MunyratanakBrorn/Smart-Electrical-Energy-Management-System/Hardware/SmartEnergyMag_System PCB deisgn/12.png

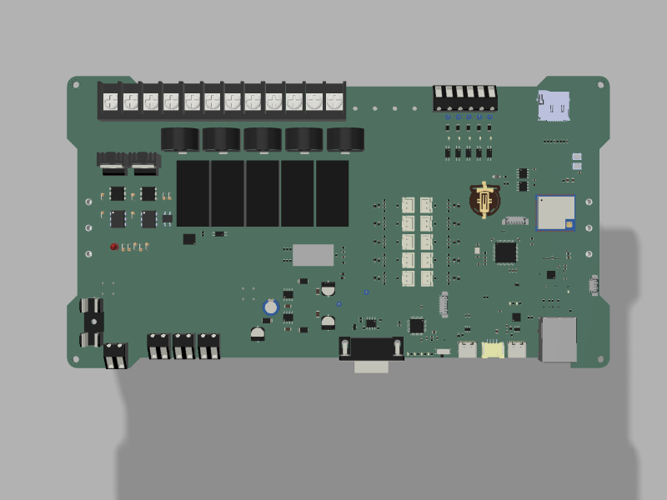
Hardware/SmartEnergyMag_System PCB deisgn/12.png
