MunyratanakBrorn/Smart-Electrical-Energy-Management-System/Hardware/SmartEnergyMag_System PCB deisgn/23.png

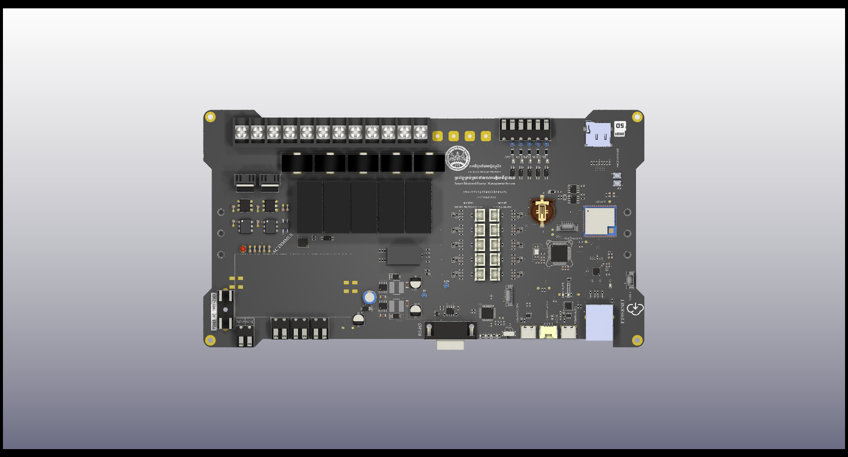
Hardware/SmartEnergyMag_System PCB deisgn/23.png
