MunyratanakBrorn/Smart-Electrical-Energy-Management-System/Hardware/SmartEnergyMag_System PCB deisgn/33.png

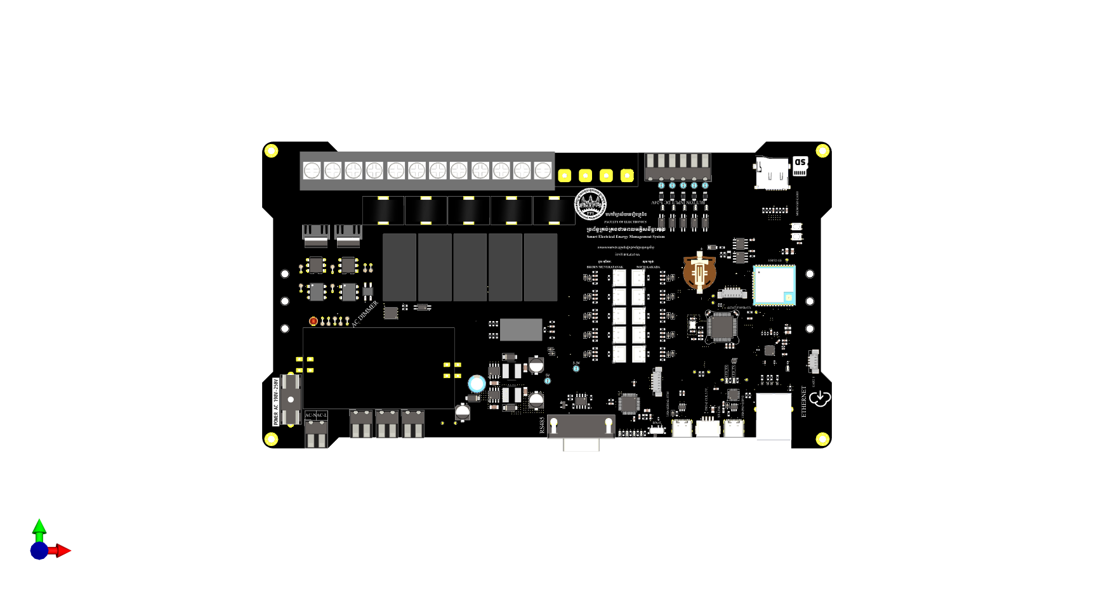
Hardware/SmartEnergyMag_System PCB deisgn/33.png
