MunyratanakBrorn/Smart-Electrical-Energy-Management-System/Hardware/SmartEnergyMag_System PCB deisgn/66.png

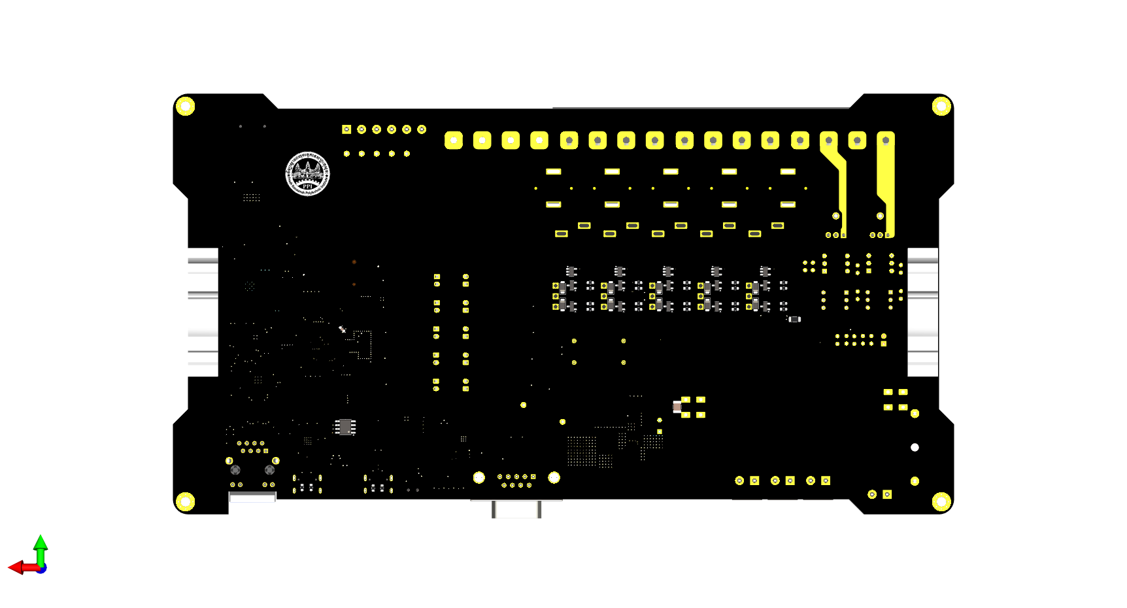
Hardware/SmartEnergyMag_System PCB deisgn/66.png
