MunyratanakBrorn/Smart-Electrical-Energy-Management-System/Hardware/SmartEnergyMag_System PCB deisgn/77.png

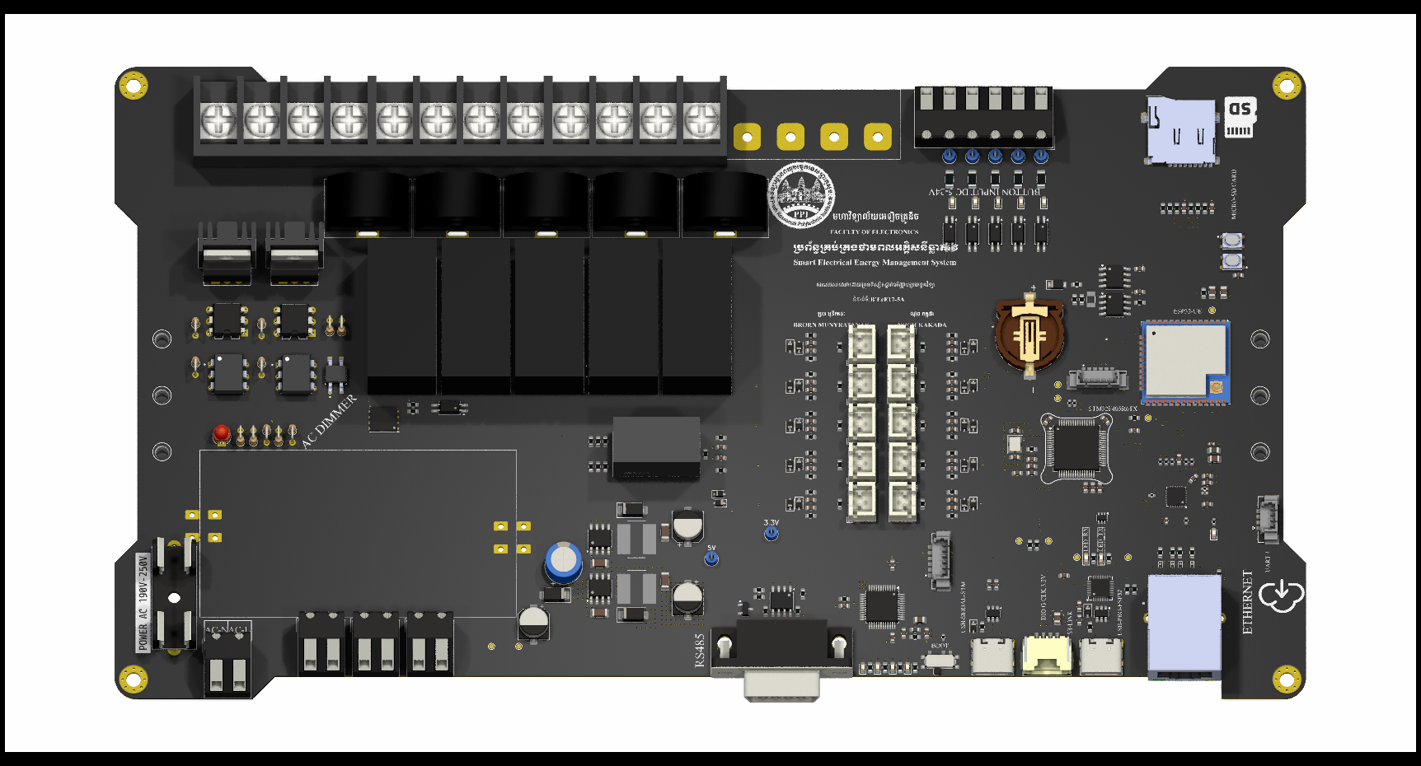
Hardware/SmartEnergyMag_System PCB deisgn/77.png
