MunyratanakBrorn/Smart-Electrical-Energy-Management-System/Hardware/SmartEnergyMag_System PCB deisgn/SmartEnergyMag_System4.png

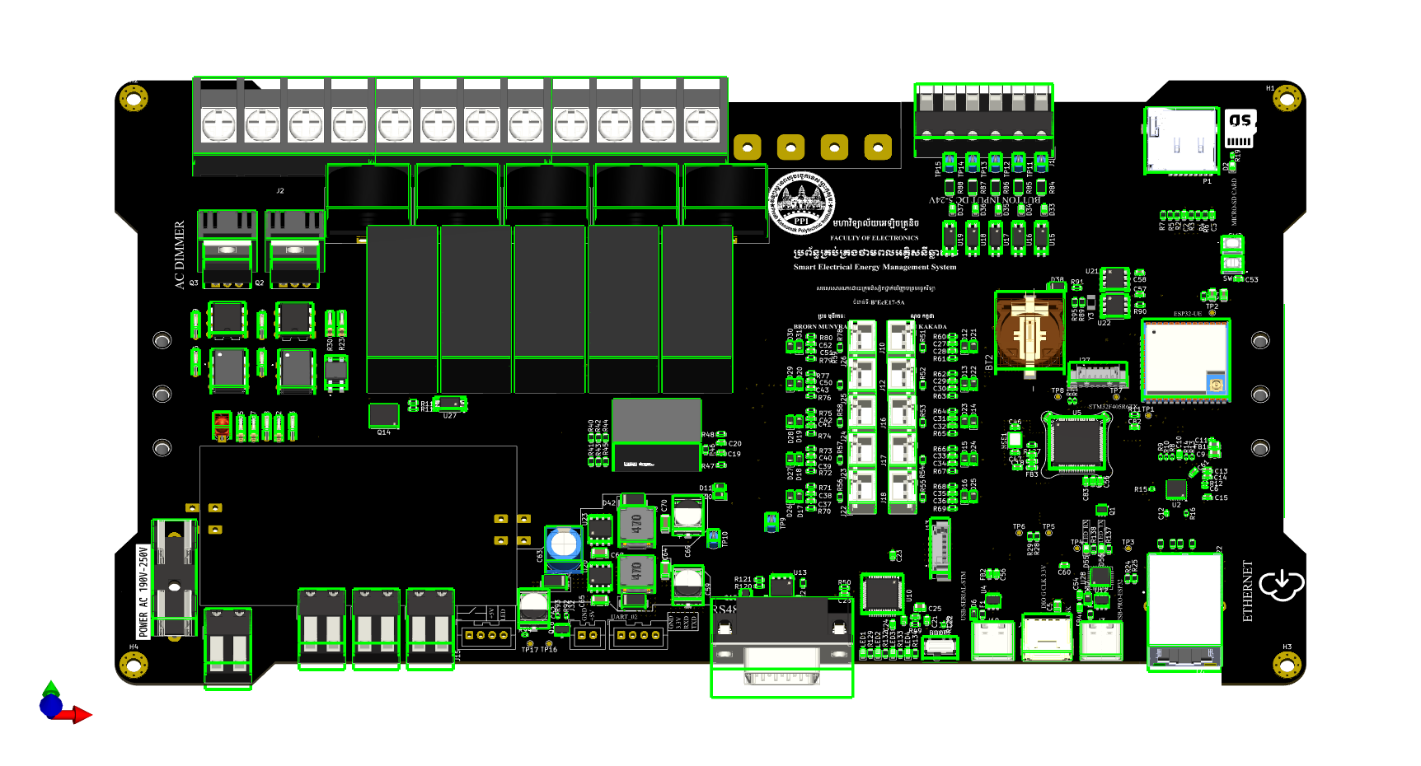
Hardware/SmartEnergyMag_System PCB deisgn/SmartEnergyMag_System4.png
