MunyratanakBrorn/Smart-Electrical-Energy-Management-System/System Overview/Hardware specification.png

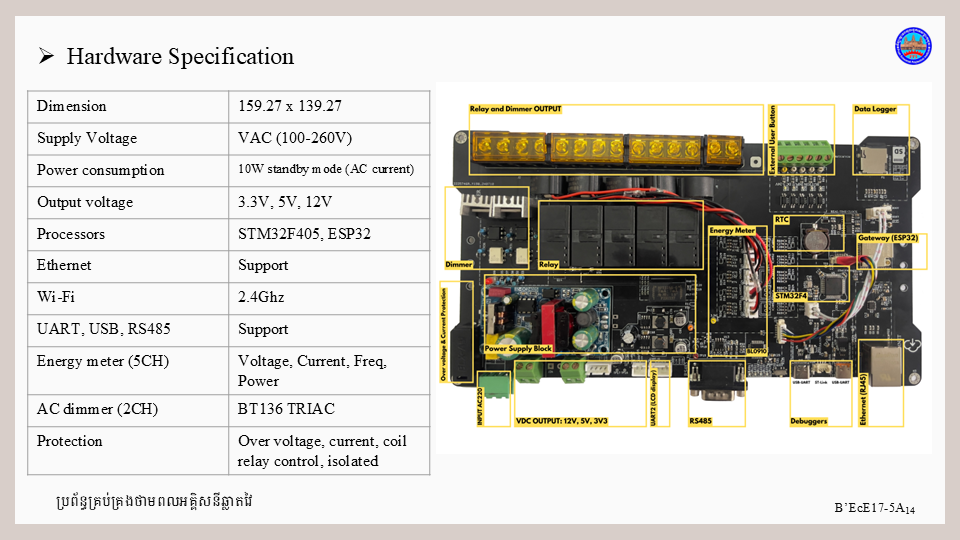
System Overview/Hardware specification.png
