MunyratanakBrorn/Smart-Electrical-Energy-Management-System/Hardware/SmartEnergyMag_System PCB deisgn/BL0940.kicad_sch

## KiCad design Hardware/SmartEnergyMag_System PCB deisgn/BL0940.kicad_sch (2024-08-28)

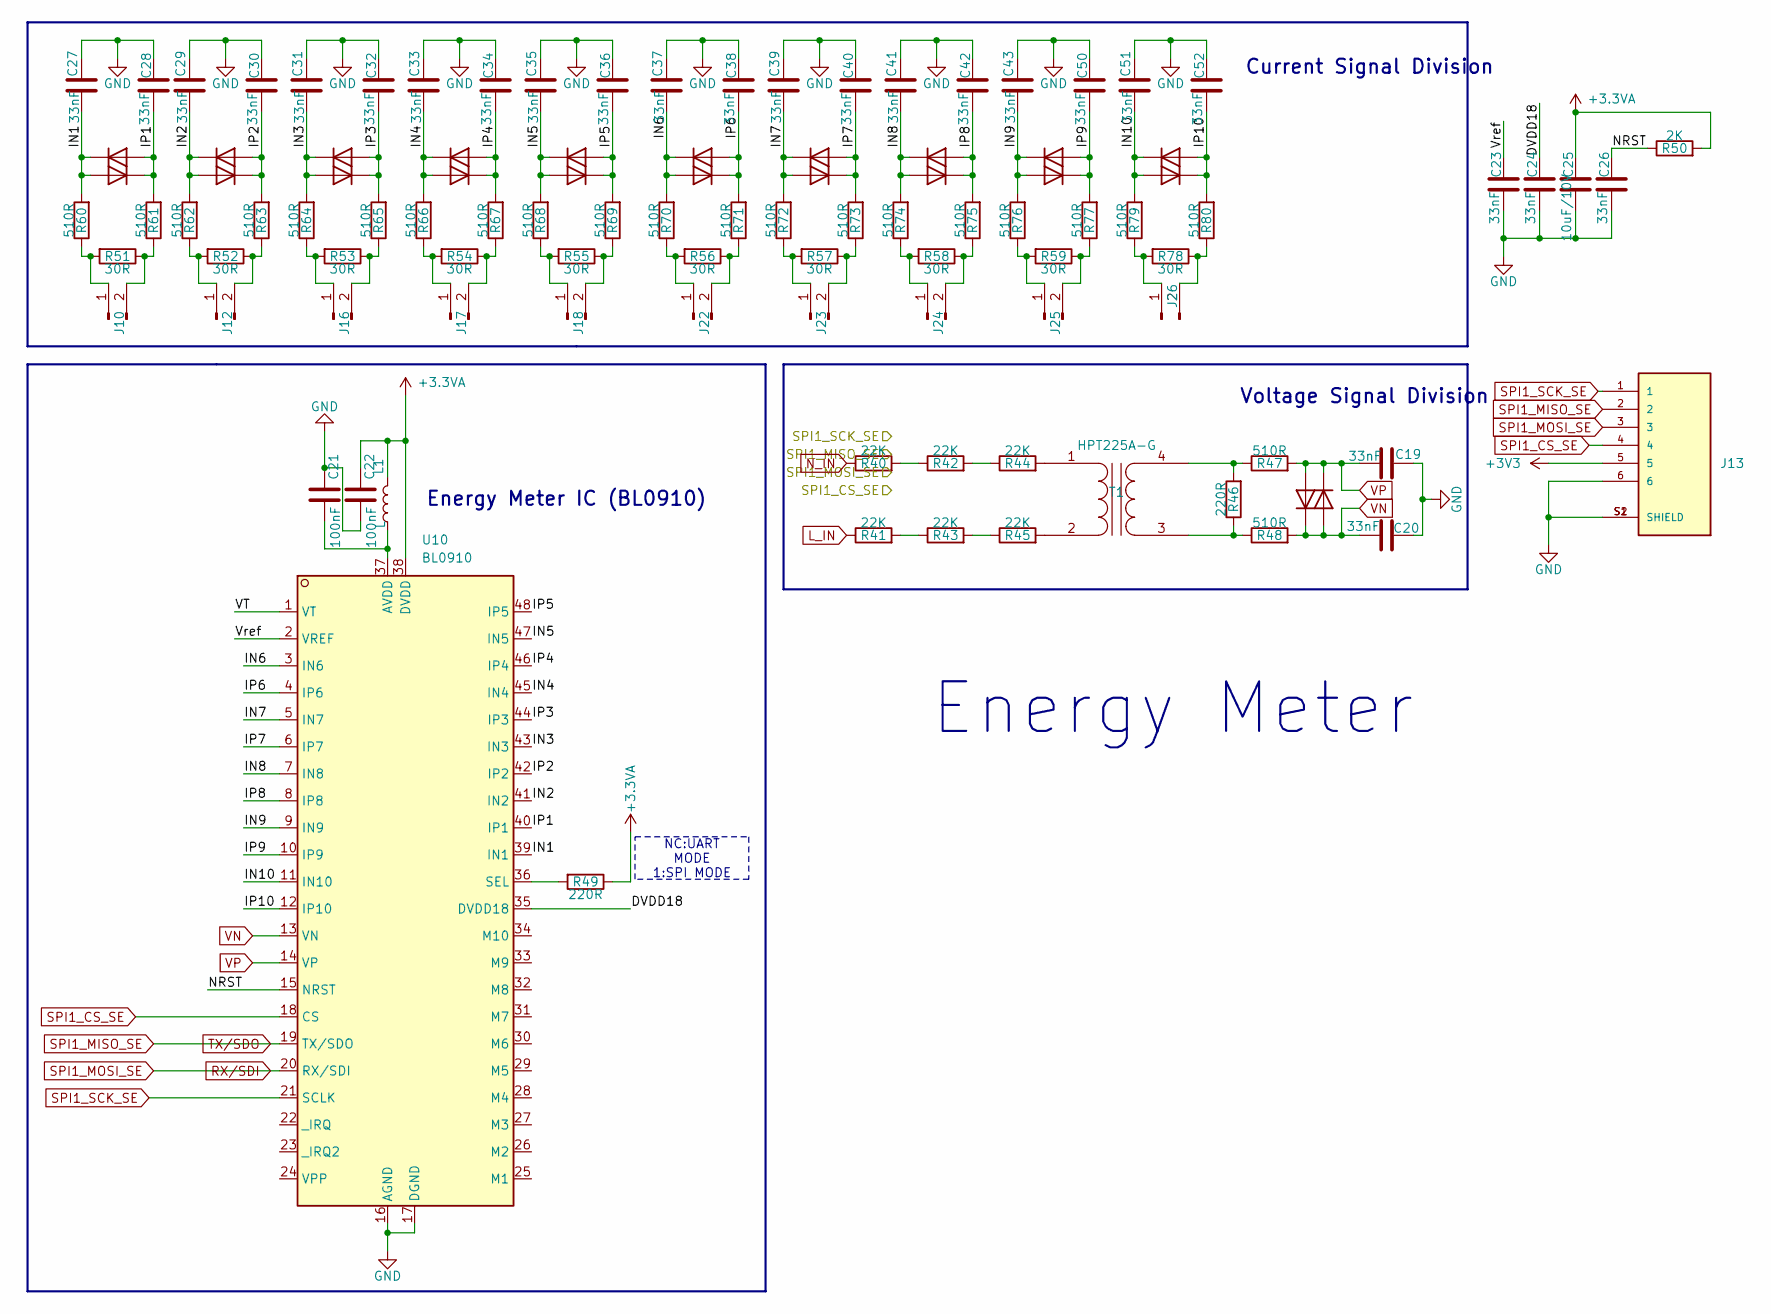
[picture p52: schematic BL0940.kicad_sch]

Parts:
C19, C20, C23, C24, C26, C27, C28, C29, C30, C31, C32, C33, C34, C35, C36, C37, C38, C39, C40, C41, C42, C43, C50, C51, C52: 33nF; C_0603_1608Metric
C21, C22: 100nF; C_0603_1608Metric
C25: 10uF/10V; C_0805_2012Metric
D10, D11, D12, D13, D14, D15, D16, D17, D18, D19, D20, D21, D22, D23, D24, D25, D26, D27, D28, D29, D30, D31: 1N4148WS; D_SOD-323
J10, J12, J16, J17, J18, J22, J23, J24, J25, J26: Conn_01x02_Pin; JST_XH_B2B-XH-A_1x02_P2.50mm_Vertical
J13: 0533980671; MOLEX_0533980671; PARTREV A
L1: L; L_0603_1608Metric
R40, R41, R42, R43, R44, R45: 22K; R_0603_1608Metric
R46, R49: 220R; R_0603_1608Metric
R47, R48, R60, R61, R62, R63, R64, R65, R66, R67, R68, R69, R70, R71, R72, R73, R74, R75, R76, R77, R79, R80: 510R; R_0603_1608Metric
R50: 2K; R_0603_1608Metric
R51, R52, R53, R54, R55, R56, R57, R58, R59, R78: 30R; R_0603_1608Metric
T1: HPT225A-G
U10: BL0910; LQFP-48_7x7mm_P0.5mm

Connections:
+3.3VA: C22.1, C25.2, L1.2, R49.1, R50.2, U10.38 (DVDD)
+3V3: J13.5
DVDD18: C24.2, U10.35 (DVDD18)
GND: C19.2, C20.2, C21.1, C22.2, C23.1, C24.1, C25.1, C26.1, C27.2, C28.2, C29.2, C30.2, C31.2, C32.2, C33.2, C34.2, C35.2, C36.2, C37.2, C38.2, C39.2, C40.2, C41.2, C42.2, C43.2, C50.2, C51.2, C52.2, J13.6, J13.S1 (SHIELD), J13.S2 (SHIELD), U10.16 (AGND), U10.17 (DGND)
IN1: C27.1, D12.2 (A), D21.1 (K), R60.2, U10.39 (IN1)
IN2: C29.1, D13.2 (A), D22.1 (K), R62.2, U10.41 (IN2)
IN3: C31.1, D14.2 (A), D23.1 (K), R64.2, U10.43 (IN3)
IN4: C33.1, D15.2 (A), D24.1 (K), R66.2, U10.45 (IN4)
IN5: C35.1, D16.2 (A), D25.1 (K), R68.2, U10.47 (IN5)
IN6: C37.1, D17.2 (A), D26.1 (K), R70.2, U10.3 (IN6)
IN7: C39.1, D18.2 (A), D27.1 (K), R72.2, U10.5 (IN7)
IN8: C41.1, D19.2 (A), D28.1 (K), R74.2, U10.7 (IN8)
IN9: C43.1, D20.2 (A), D29.1 (K), R76.2, U10.9 (IN9)
IN10: C51.1, D30.2 (A), D31.1 (K), R79.2, U10.11 (IN10)
IP1: C28.1, D12.1 (K), D21.2 (A), R61.2, U10.40 (IP1)
IP2: C30.1, D13.1 (K), D22.2 (A), R63.2, U10.42 (IP2)
IP3: C32.1, D14.1 (K), D23.2 (A), R65.2, U10.44 (IP3)
IP4: C34.1, D15.1 (K), D24.2 (A), R67.2, U10.46 (IP4)
IP5: C36.1, D16.1 (K), D25.2 (A), R69.2, U10.48 (IP5)
IP6: C38.1, D17.1 (K), D26.2 (A), R71.2, U10.4 (IP6)
IP7: C40.1, D18.1 (K), D27.2 (A), R73.2, U10.6 (IP7)
IP8: C42.1, D19.1 (K), D28.2 (A), R75.2, U10.8 (IP8)
IP9: C50.1, D20.1 (K), D29.2 (A), R77.2, U10.10 (IP9)
IP10: C52.1, D30.1 (K), D31.2 (A), R80.2, U10.12 (IP10)
L_IN: R41.1
NRST: C26.2, R50.1, U10.15 (NRST)
N_IN: R40.1
unnamed: C21.2, L1.1, U10.37 (AVDD)
unnamed: J10.1, R51.2, R60.1
unnamed: J10.2, R51.1, R61.1
unnamed: J12.1, R52.2, R62.1
unnamed: J12.2, R52.1, R63.1
unnamed: J16.1, R53.2, R64.1
unnamed: J16.2, R53.1, R65.1
unnamed: J17.1, R54.2, R66.1
unnamed: J17.2, R54.1, R67.1
unnamed: J18.1, R55.2, R68.1
unnamed: J18.2, R55.1, R69.1
unnamed: J22.1, R56.2, R70.1
unnamed: J22.2, R56.1, R71.1
unnamed: J23.1, R57.2, R72.1
unnamed: J23.2, R57.1, R73.1
unnamed: J24.1, R58.2, R74.1
unnamed: J24.2, R58.1, R75.1
unnamed: J25.1, R59.2, R76.1
unnamed: J25.2, R59.1, R77.1
unnamed: J26.1, R78.2, R79.1
unnamed: J26.2, R78.1, R80.1
unnamed: R40.2, R42.1
unnamed: R41.2, R43.1
unnamed: R42.2, R44.1
unnamed: R43.2, R45.1
unnamed: R44.2, T1.1 (AA)
unnamed: R45.2, T1.2 (AB)
unnamed: R46.1, R48.1, T1.3 (SA)
unnamed: R46.2, R47.1, T1.4 (SB)
unnamed: R49.2, U10.36 (SEL)
RX/SDI: J13.3, U10.20 (RX/SDI)
SPI1_CS_SE: J13.4, U10.18 (CS)
SPI1_MISO_SE: J13.2, U10.19 (TX/SDO)
SPI1_SCK_SE: J13.1, U10.21 (SCLK)
VN: C20.1, D10.1 (K), D11.2 (A), R48.2, U10.13 (VN)
VP: C19.1, D10.2 (A), D11.1 (K), R47.2, U10.14 (VP)
VT: U10.1 (VT)
Vref: C23.2, U10.2 (VREF)

Notes on the sheet:
NC:UART MODE 1:SPI MODE
Energy Meter
Voltage Signal Division
Current Signal Division
Energy Meter IC (BL0910)
