MunyratanakBrorn/Smart-Electrical-Energy-Management-System/Hardware/SmartEnergyMag_System PCB deisgn/BL0940_4,5.kicad_sch

## KiCad design Hardware/SmartEnergyMag_System PCB deisgn/BL0940_4,5.kicad_sch (2024-08-28)

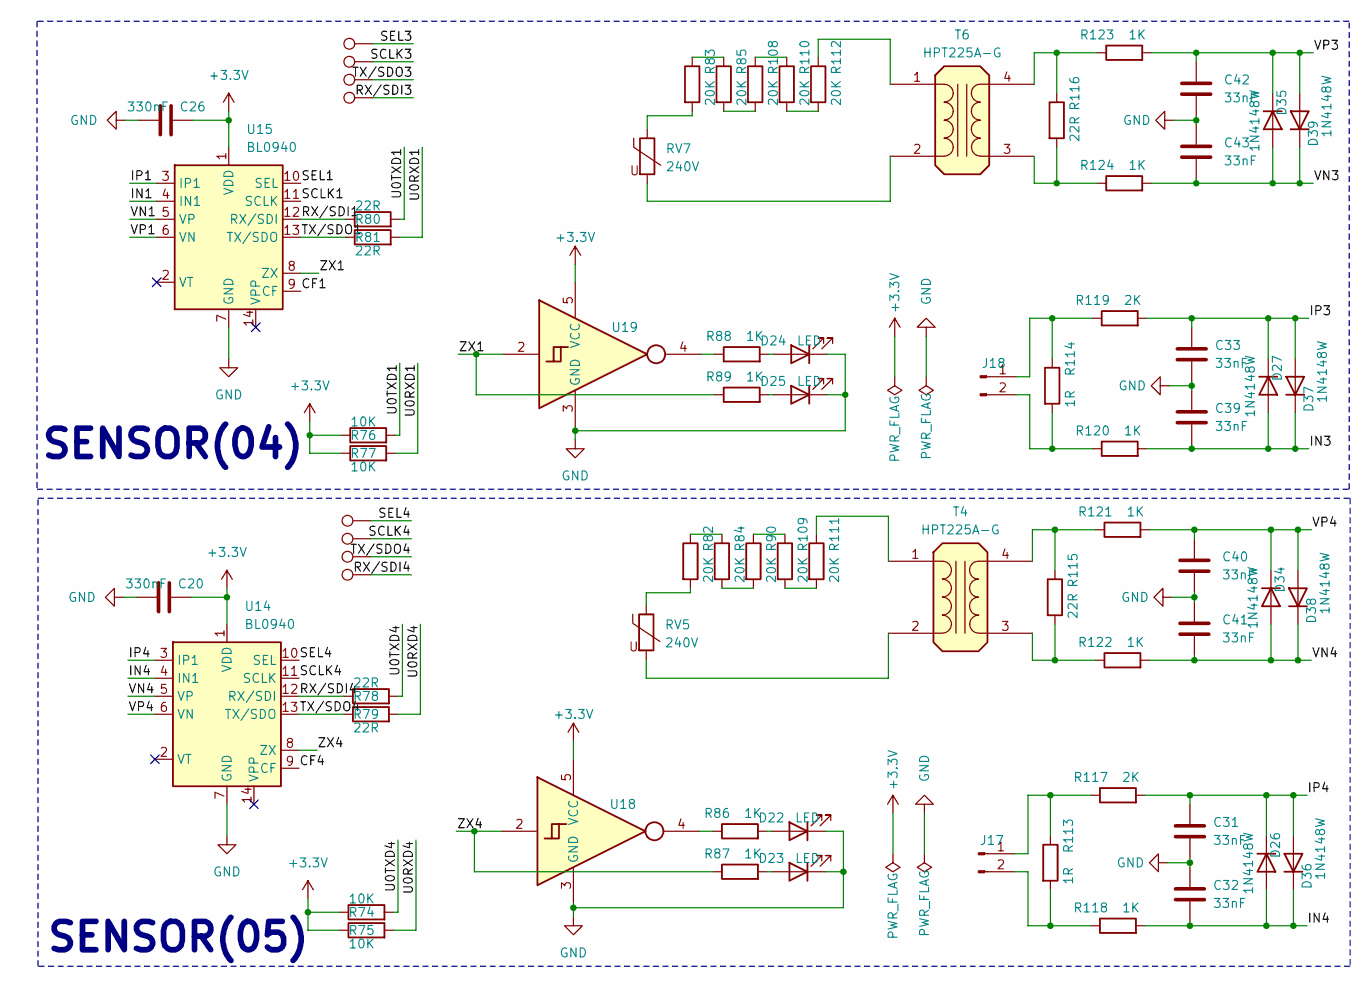
[picture p53: schematic BL0940_4,5.kicad_sch]

Parts:
C20, C26: 330nF; C_0805_2012Metric
C31, C32, C33, C39, C40, C41, C42, C43: 33nF; C_0603_1608Metric
D22, D23, D24, D25: LED; LED_0603_1608Metric
D26, D27, D34, D35, D36, D37, D38, D39: 1N4148W; D_SOD-323
J17, J18: Conn_01x02_Pin; JST_EH_B2B-EH-A_1x02_P2.50mm_Vertical
R74, R75, R76, R77: 10K; R_0603_1608Metric
R78, R79, R80, R81, R115, R116: 22R; R_0603_1608Metric
R82, R83, R84, R85, R90, R108, R109, R110, R111, R112: 20K; R_0603_1608Metric
R86, R87, R88, R89, R118, R120, R121, R122, R123, R124: 1K; R_0603_1608Metric
R113, R114: 1R; R_0603_1608Metric
R117, R119: 2K; R_0603_1608Metric
RV5, RV7: 240V; RV_Disc_D7mm_W3.5mm_P5mm
T4, T6: HPT225A-G
TP13, TP14, TP15, TP16, TP17, TP18, TP25, TP26: TestPoint; TestPoint_Pad_D1.5mm
U14, U15: BL0940; TSSOP-14_4.4x5mm_P0.65mm
U18, U19: SN74LVC1G14DBV; SOT-23-5

Connections:
+3.3V: C20.2, C26.2, R74.1, R75.1, R76.1, R77.1, U14.1 (VDD), U15.1 (VDD), U18.5 (VCC), U19.5 (VCC)
CF1: U15.9 (CF)
CF4: U14.9 (CF)
GND: C20.1, C26.1, C31.2, C32.1, C33.2, C39.1, C40.2, C41.1, C42.2, C43.1, D22.1 (K), D23.1 (K), D24.1 (K), D25.1 (K), U14.7 (GND), U15.7 (GND), U18.3 (GND), U19.3 (GND)
IN1: U15.4 (IN1)
IN3: C39.2, D27.2 (A), D37.1 (K), R120.2
IN4: C32.2, D26.2 (A), D36.1 (K), R118.2, U14.4 (IN1)
IP1: U15.3 (IP1)
IP3: C33.1, D27.1 (K), D37.2 (A), R119.2
IP4: C31.1, D26.1 (K), D36.2 (A), R117.2, U14.3 (IP1)
unnamed: D22.2 (A), R86.2
unnamed: D23.2 (A), R87.2
unnamed: D24.2 (A), R88.2
unnamed: D25.2 (A), R89.2
unnamed: J17.1, R113.1, R117.1
unnamed: J17.2, R113.2, R118.1
unnamed: J18.1, R114.1, R119.1
unnamed: J18.2, R114.2, R120.1
unnamed: R82.1, R84.1
unnamed: R82.2, RV5.1
unnamed: R83.1, R85.1
unnamed: R83.2, RV7.1
unnamed: R84.2, R90.2
unnamed: R86.1, U18.4
unnamed: R88.1, U19.4
unnamed: R108.1, R110.1
unnamed: R85.2, R108.2
unnamed: R90.1, R109.1
unnamed: R109.2, R111.2
unnamed: R110.2, R112.2
unnamed: R111.1, T4.1 (AA)
unnamed: R112.1, T6.1 (AA)
unnamed: R115.1, R121.1, T4.4 (SB)
unnamed: R115.2, R122.1, T4.3 (SA)
unnamed: R116.1, R123.1, T6.4 (SB)
unnamed: R116.2, R124.1, T6.3 (SA)
unnamed: RV5.2, T4.2 (AB)
unnamed: RV7.2, T6.2 (AB)
RX/SDI1: R80.1, U15.12 (RX/SDI)
RX/SDI3: TP26.1
RX/SDI4: R78.1, TP16.1, U14.12 (RX/SDI)
SCLK1: U15.11 (SCLK)
SCLK3: TP18.1
SCLK4: TP14.1, U14.11 (SCLK)
SEL1: U15.10 (SEL)
SEL3: TP17.1
SEL4: TP13.1, U14.10 (SEL)
TX/SDO1: R81.1, U15.13 (TX/SDO)
TX/SDO3: TP25.1
TX/SDO4: R79.1, TP15.1, U14.13 (TX/SDO)
U0RXD1: R77.2, R81.2
U0RXD4: R75.2, R79.2
U0TXD1: R76.2, R80.2
U0TXD4: R74.2, R78.2
VN1: U15.5 (VP)
VN3: C43.2, D35.2 (A), D39.1 (K), R124.2
VN4: C41.2, D34.2 (A), D38.1 (K), R122.2, U14.5 (VP)
VP1: U15.6 (VN)
VP3: C42.1, D35.1 (K), D39.2 (A), R123.2
VP4: C40.1, D34.1 (K), D38.2 (A), R121.2, U14.6 (VN)
ZX1: R89.1, U15.8 (ZX), U19.2
ZX4: R87.1, U14.8 (ZX), U18.2

Notes on the sheet:
SENSOR(05)
SENSOR(04)
