MunyratanakBrorn/Smart-Electrical-Energy-Management-System/Hardware/SmartEnergyMag_System PCB deisgn/BUTTON-INPUT.kicad_sch

## KiCad design Hardware/SmartEnergyMag_System PCB deisgn/BUTTON-INPUT.kicad_sch (2024-08-28)

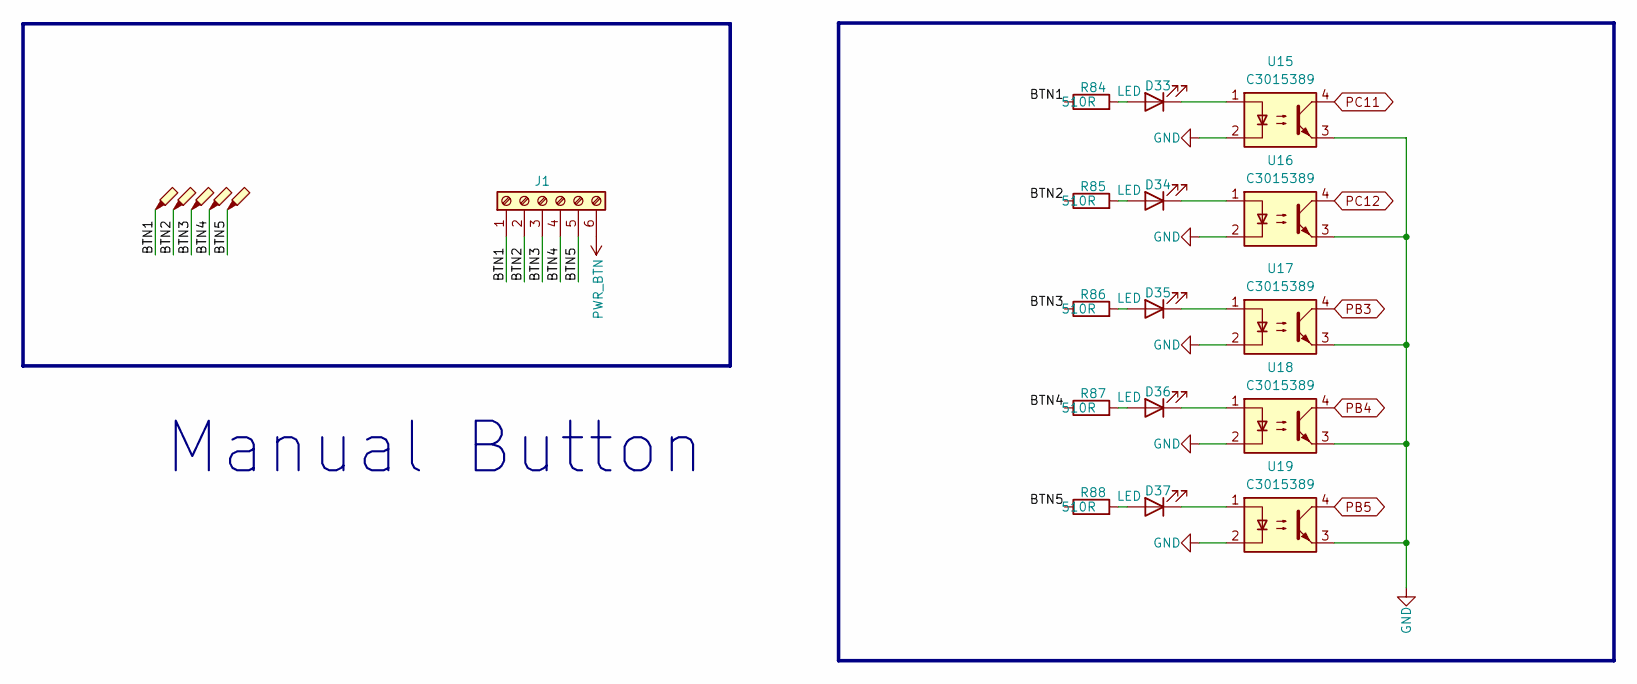
[picture p54: schematic BUTTON-INPUT.kicad_sch]

Parts:
D33, D34, D35, D36, D37: LED; LED_0603_1608Metric
J1: Screw_Terminal_01x06; Altech_AK300_1x06_P5.00mm_45-Degree
R84, R85, R86, R87, R88: 510R; R_1206_3216Metric; JLCPCB Part # C3017298
TP11, TP13, TP14, TP15: C5199900; TestPoint_Loop_D1.80mm_Drill1.0mm_Beaded; JLCPCB Part # C5277087
TP12: C5199900; TestPoint_Loop_D1.80mm_Drill1.0mm_Beaded
U15, U16, U17, U18, U19: C3015389; SOP-4_4.4x2.6mm_P1.27mm

Connections:
BTN1: J1.1, R84.1, TP11.1
BTN2: J1.2, R85.1, TP12.1
BTN3: J1.3, R86.1, TP13.1
BTN4: J1.4, R87.1, TP14.1
BTN5: J1.5, R88.1, TP15.1
GND: U15.2, U15.3, U16.2, U16.3, U17.2, U17.3, U18.2, U18.3, U19.2, U19.3
unnamed: D33.1 (K), U15.1
unnamed: D33.2 (A), R84.2
unnamed: D34.1 (K), U16.1
unnamed: D34.2 (A), R85.2
unnamed: D35.1 (K), U17.1
unnamed: D35.2 (A), R86.2
unnamed: D36.1 (K), U18.1
unnamed: D36.2 (A), R87.2
unnamed: D37.1 (K), U19.1
unnamed: D37.2 (A), R88.2
PB3: U17.4
PB4: U18.4
PB5: U19.4
PC11: U15.4
PC12: U16.4
PWR_BTN: J1.6

Notes on the sheet:
Manual Button
