MunyratanakBrorn/Smart-Electrical-Energy-Management-System/Hardware/SmartEnergyMag_System PCB deisgn/Buck converter.kicad_sch

## KiCad design Hardware/SmartEnergyMag_System PCB deisgn/Buck converter.kicad_sch (2024-08-28)

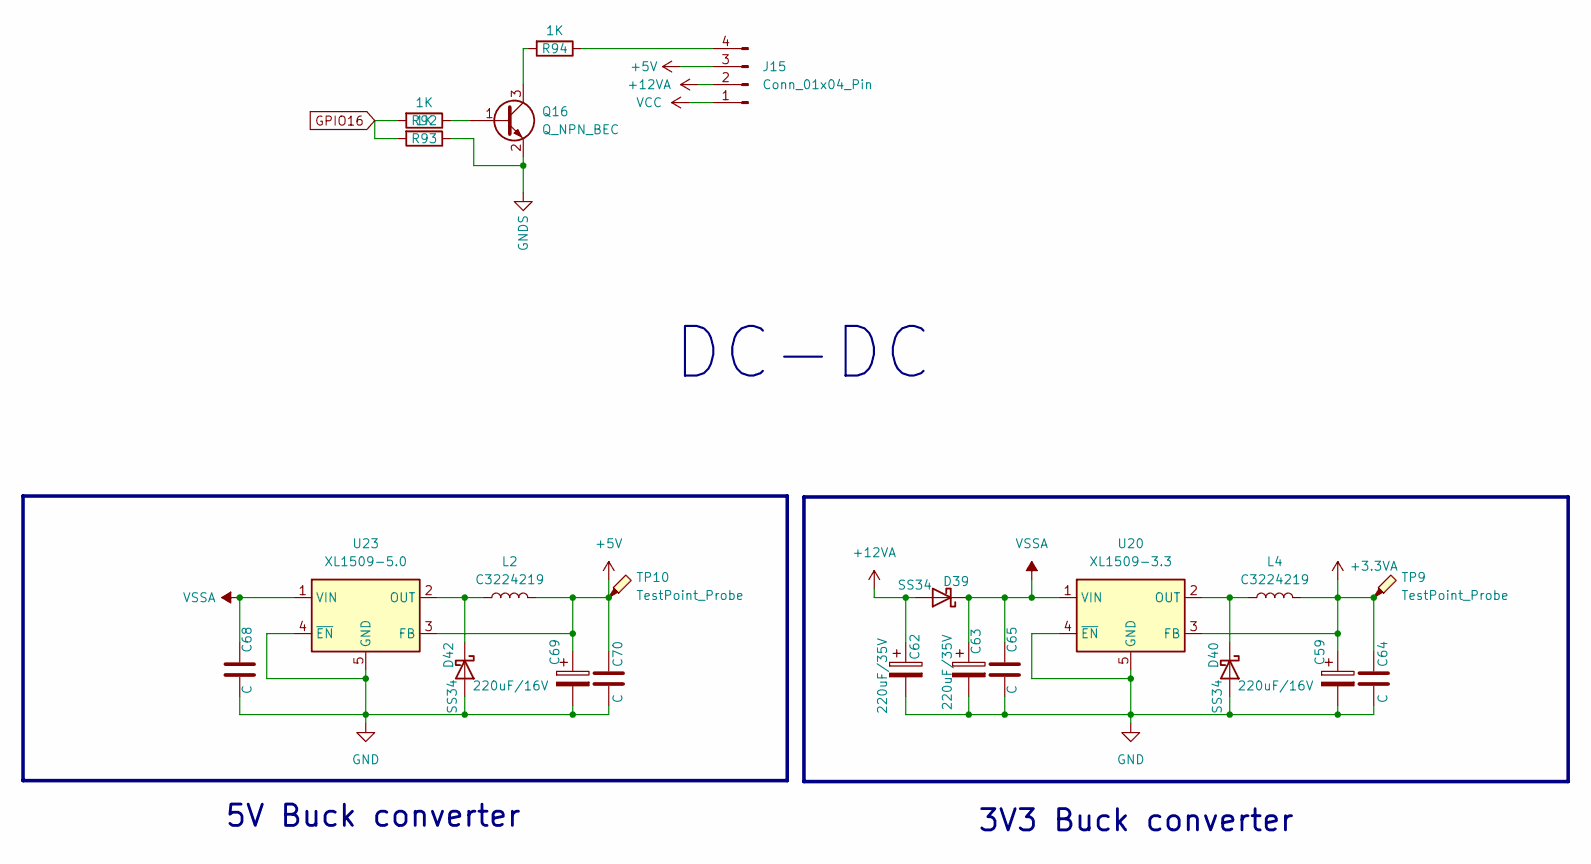
[picture p55: schematic Buck converter.kicad_sch]

Parts:
C59, C69: 220uF/16V; CP_Elec_6.3x4.5; JLCPCB Part # C59918
C62: 220uF/35V; CP_Elec_6.3x4.5; JLCPCB Part # C59918
C63: 220uF/35V; CP_Radial_D8.0mm_P3.80mm; JLCPCB Part # C59918
C64, C65, C68, C70: C; C_1206_3216Metric
D39, D40, D42: SS34; D_SMA
J15: Conn_01x04_Pin; JST_XA_B04B-XASK-1_1x04_P2.50mm_Vertical
L2, L4: C3224219; L_Bourns_SRN8040TA
Q16: Q_NPN_BEC; SOT-23
R92, R93, R94: 1K; R_0402_1005Metric
TP9, TP10: TestPoint_Probe; TestPoint_Loop_D1.80mm_Drill1.0mm_Beaded
U20: XL1509-3.3; SOIC-8_3.9x4.9mm_P1.27mm; JLCPCB Part # C2681226
U23: XL1509-5.0; SOIC-8_3.9x4.9mm_P1.27mm; JLCPCB Part # C2902368

Connections:
+3.3VA: C59.1, C64.1, L4.2, TP9.1, U20.3 (FB)
+5V: C69.1, C70.1, J15.3, L2.2, TP10.1, U23.3 (FB)
+12VA: C62.1, D39.2 (A), J15.2
GND: C59.2, C62.2, C63.2, C64.2, C65.2, C68.2, C69.2, C70.2, D40.2 (A), D42.2 (A), U20.4 (~EN), U20.5 (GND), U20.6 (GND), U20.7 (GND), U20.8 (GND), U23.4 (~EN), U23.5 (GND), U23.6 (GND), U23.7 (GND), U23.8 (GND)
GNDS: Q16.2 (E), R93.1
GPIO16: R92.2, R93.2
unnamed: D40.1 (K), L4.1, U20.2 (OUT)
unnamed: D42.1 (K), L2.1, U23.2 (OUT)
unnamed: J15.4, R94.1
unnamed: Q16.1 (B), R92.1
unnamed: Q16.3 (C), R94.2
VCC: J15.1
VSSA: C63.1, C65.1, C68.1, D39.1 (K), U20.1 (VIN), U23.1 (VIN)

Notes on the sheet:
3V3 Buck converter
DC-DC
5V Buck converter
