MunyratanakBrorn/Smart-Electrical-Energy-Management-System/Hardware/SmartEnergyMag_System PCB deisgn/Dimmer PCB.kicad_sch

## KiCad design Hardware/SmartEnergyMag_System PCB deisgn/Dimmer PCB.kicad_sch (2024-08-28)

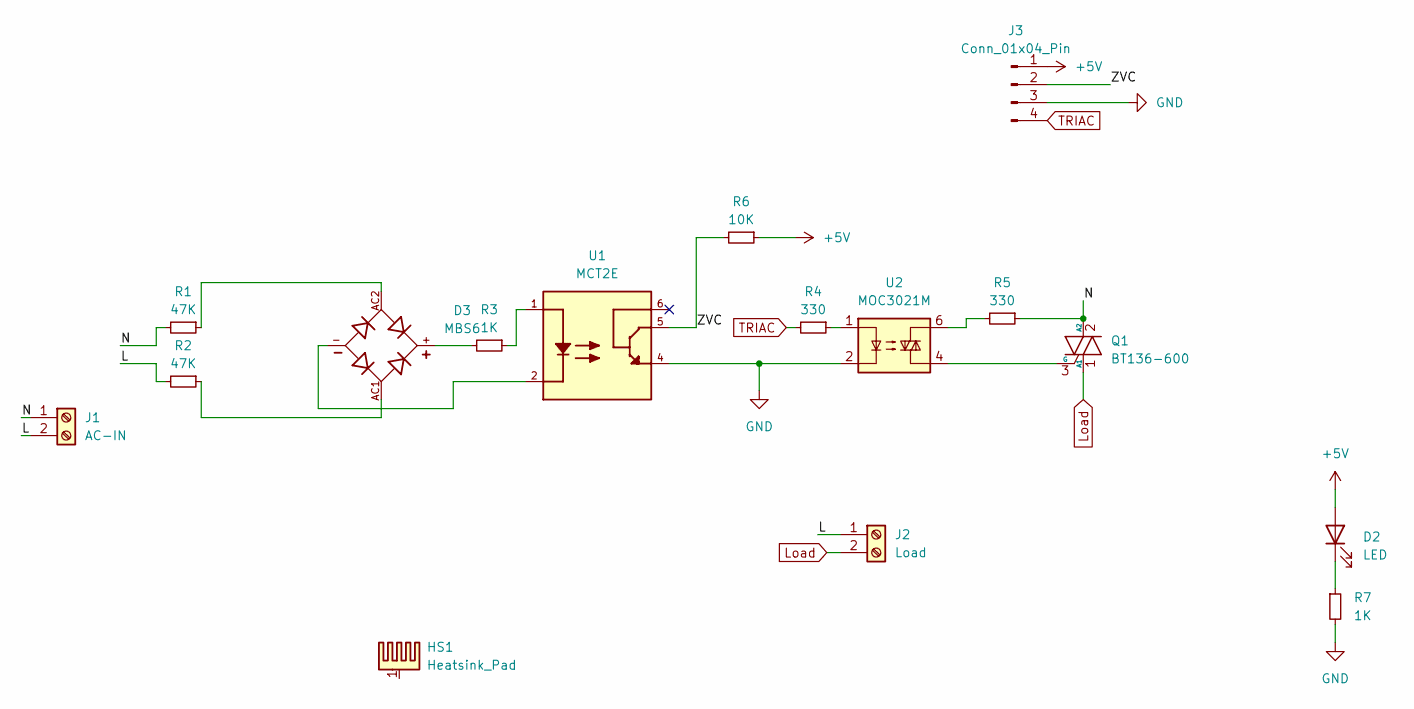
[picture p56: schematic Dimmer PCB.kicad_sch]

Parts:
D2: LED; LED_D3.0mm
D3: MBS6; DIOB_MBS6; PARTREV Q2309
HS1: Heatsink_Pad; HSINK_SK_95_25_STS_TO_220
J1: AC-IN; Altech_AK300_1x02_P5.00mm_45-Degree
J2: Load; Altech_AK300_1x02_P5.00mm_45-Degree
J3: Conn_01x04_Pin; PinHeader_1x04_P2.54mm_Vertical
Q1: BT136-600; TO-220-3_Vertical
R1, R2: 47K; R_Axial_DIN0204_L3.6mm_D1.6mm_P2.54mm_Vertical
R3, R7: 1K; R_Axial_DIN0204_L3.6mm_D1.6mm_P2.54mm_Vertical
R4, R5: 330; R_Axial_DIN0204_L3.6mm_D1.6mm_P2.54mm_Vertical
R6: 10K; R_Axial_DIN0204_L3.6mm_D1.6mm_P2.54mm_Vertical
U1: MCT2E; DIP762W50P254L742H480Q6; PARTREV 7
U2: MOC3021M; DIP-6_W7.62mm

Connections:
+5V: D2.2 (A), J3.1, R6.1
GND: J3.3, R7.2, U1.4, U2.2
L: J1.2, J2.1, R2.2
Load: J2.2, Q1.1 (A1)
N: J1.1, Q1.2 (A2), R1.2, R5.1
unnamed: D2.1 (K), R7.1
unnamed: D3.+, R3.2
unnamed: D3.-, U1.2
unnamed: D3.AC1, R2.1
unnamed: D3.AC2, R1.1
unnamed: Q1.3 (G), U2.4
unnamed: R3.1, U1.1
unnamed: R4.1, U2.1
unnamed: R5.2, U2.6
TRIAC: J3.4, R4.2
ZVC: J3.2, R6.2, U1.5
