MunyratanakBrorn/Smart-Electrical-Energy-Management-System/Hardware/SmartEnergyMag_System PCB deisgn/Dimmer_PCB.kicad_sch

## KiCad design Hardware/SmartEnergyMag_System PCB deisgn/Dimmer_PCB.kicad_sch (2024-08-28)

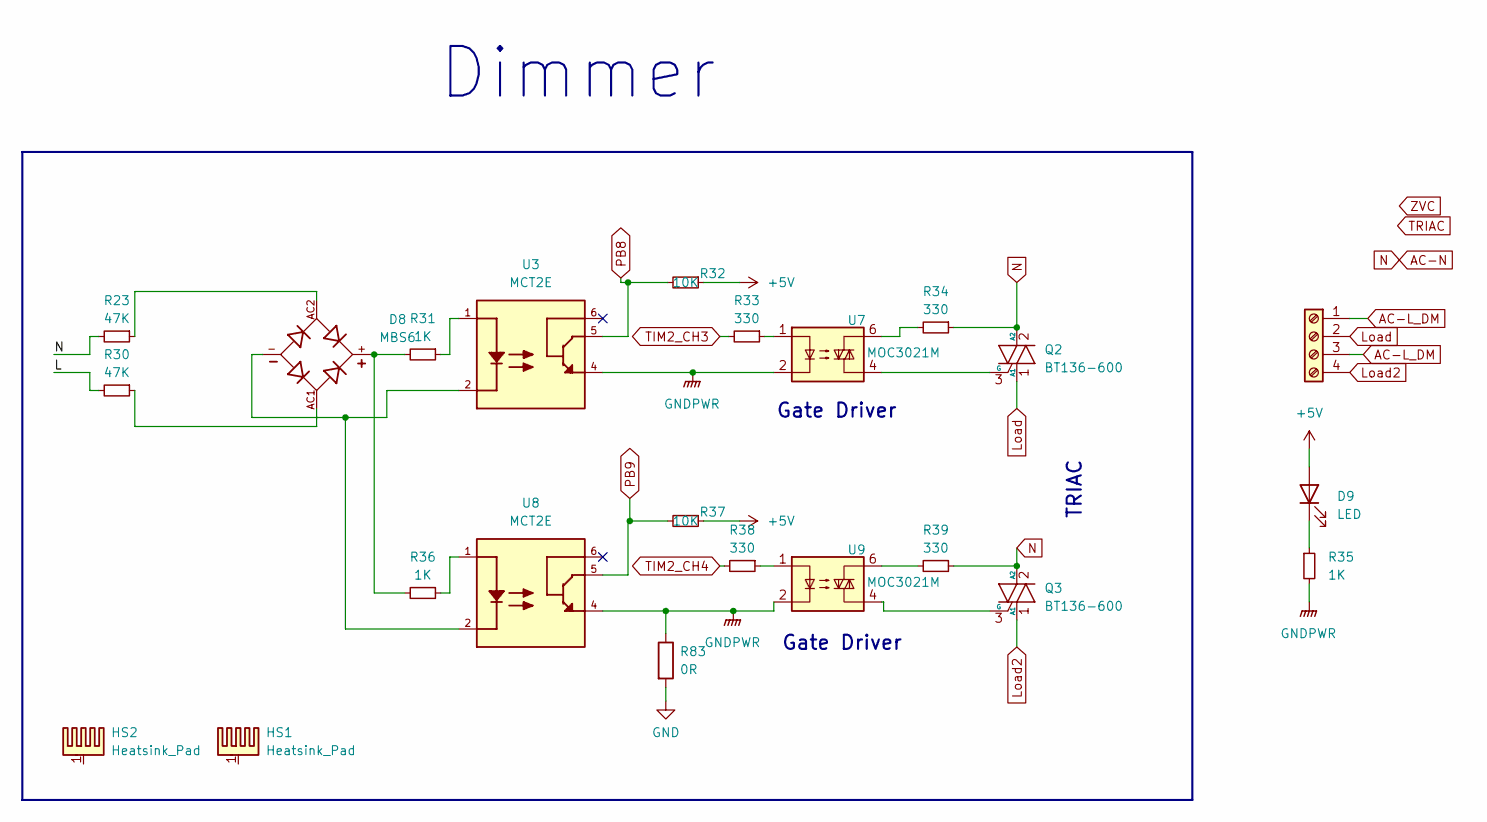
[picture p57: schematic Dimmer_PCB.kicad_sch]

Parts:
D8: MBS6; DIOB_MBS6; PARTREV Q2309
D9: LED; LED_D3.0mm
HS1, HS2: Heatsink_Pad; HSINK_SK_95_25_STS_TO_220
J2: Screw_Terminal_01x04; DBT50G-9.5-4P
Q2, Q3: BT136-600; TO-220-3_Vertical
R23, R30: 47K; R_Axial_DIN0204_L3.6mm_D1.6mm_P2.54mm_Vertical
R31, R35, R36: 1K; R_Axial_DIN0204_L3.6mm_D1.6mm_P2.54mm_Vertical
R32, R37: 10K; R_Axial_DIN0204_L3.6mm_D1.6mm_P2.54mm_Vertical
R33, R34, R38, R39: 330; R_Axial_DIN0204_L3.6mm_D1.6mm_P2.54mm_Vertical
R83: 0R; R_1206_3216Metric
U3, U8: MCT2E; DIP762W50P254L742H480Q6; PARTREV 7
U7, U9: MOC3021M; DIP-6_W7.62mm

Connections:
+5V: D9.2 (A), R32.1, R37.1
AC-L_DM: J2.1, J2.3
AC-N: Q2.2 (A2), Q3.2 (A2), R34.1, R39.1
GND: R83.2
GNDPWR: R35.2, R83.1, U3.4, U7.2, U8.4, U9.2
L: R30.2
Load: J2.2, Q2.1 (A1)
Load2: J2.4, Q3.1 (A1)
N: R23.2
unnamed: D8.+, R31.2, R36.2
unnamed: D8.-, U3.2, U8.2
unnamed: D8.AC1, R30.1
unnamed: D8.AC2, R23.1
unnamed: D9.1 (K), R35.1
unnamed: Q2.3 (G), U7.4
unnamed: Q3.3 (G), U9.4
unnamed: R31.1, U3.1
unnamed: R33.1, U7.1
unnamed: R34.2, U7.6
unnamed: R36.1, U8.1
unnamed: R38.1, U9.1
unnamed: R39.2, U9.6
PB8: R32.2, U3.5
PB9: R37.2, U8.5
TIM2_CH3: R33.2
TIM2_CH4: R38.2

Notes on the sheet:
TRIAC
Gate Driver
Dimmer
