MunyratanakBrorn/Smart-Electrical-Energy-Management-System/Hardware/SmartEnergyMag_System PCB deisgn/Microcontroller.kicad_sch

## KiCad design Hardware/SmartEnergyMag_System PCB deisgn/Microcontroller.kicad_sch (2024-08-28)

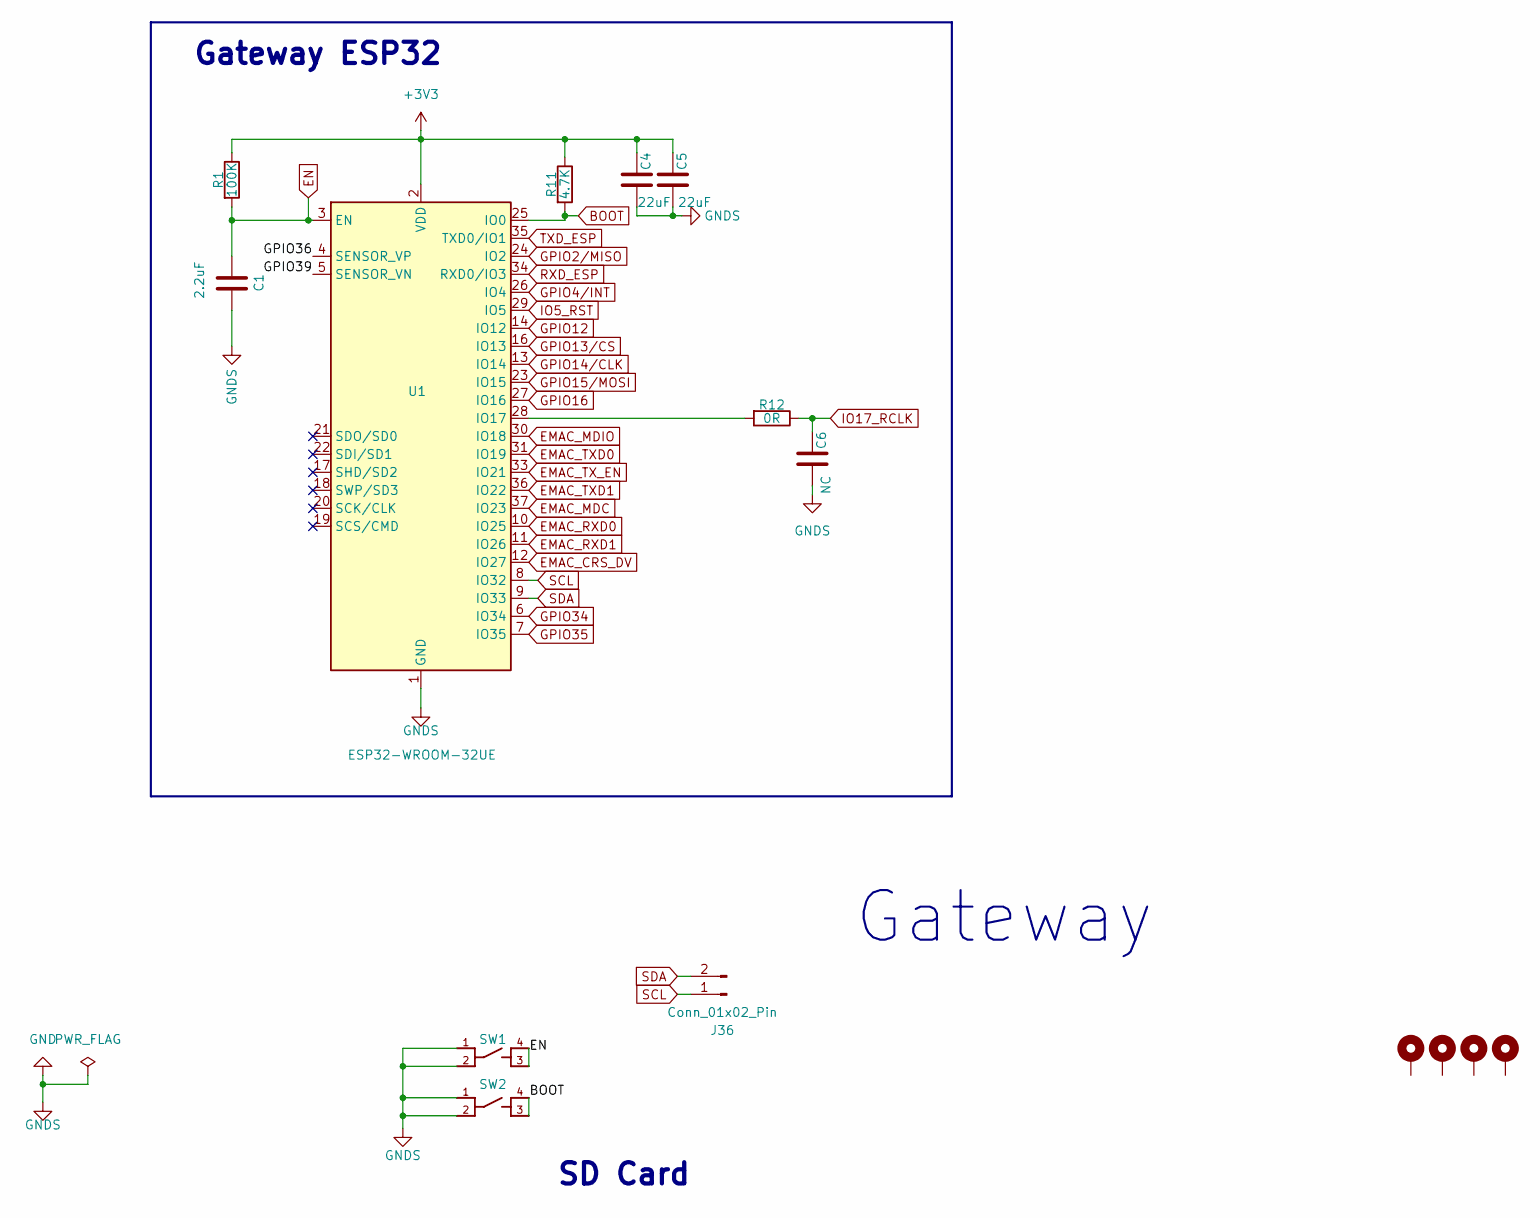
[picture p58: schematic Microcontroller.kicad_sch]

Parts:
C1: 2.2uF; C_0805_2012Metric
C4, C5: 22uF; C_0805_2012Metric
C6: NC; C_0402_1005Metric
H1, H2, H3, H4: MountingHole_Pad; MountingHole_3.2mm_M3_Pad_Via
J36: Conn_01x02_Pin; JST_XA_B02B-XASK-1_1x02_P2.50mm_Vertical
R1: 100K; R_0603_1608Metric
R11: 4.7K; R_0603_1608Metric
R12: 0R; R_0402_1005Metric
SW1, SW2: C221895; SW_PTS810_SJM_250_SMTR_LFS
U1: ESP32-WROOM-32UE; ESP32-WROOM-32U

Connections:
+3V3: C4.1, C5.1, R1.1, R11.1, U1.2 (VDD)
BOOT: R11.2, SW2.3, SW2.4, U1.25 (IO0)
EMAC_CRS_DV: U1.12 (IO27)
EMAC_MDC: U1.37 (IO23)
EMAC_MDIO: U1.30 (IO18)
EMAC_RXD0: U1.10 (IO25)
EMAC_RXD1: U1.11 (IO26)
EMAC_TXD0: U1.31 (IO19)
EMAC_TXD1: U1.36 (IO22)
EMAC_TX_EN: U1.33 (IO21)
EN: C1.1, R1.2, SW1.3, SW1.4, U1.3 (EN)
GND: C1.2, C4.2, C5.2, C6.2, SW1.1, SW1.2, SW2.1, SW2.2, U1.1 (GND), U1.15 (GND), U1.38 (GND), U1.39 (GND)
GPIO2/MISO: U1.24 (IO2)
GPIO4/INT: U1.26 (IO4)
GPIO12: U1.14 (IO12)
GPIO13/CS: U1.16 (IO13)
GPIO14/CLK: U1.13 (IO14)
GPIO15/MOSI: U1.23 (IO15)
GPIO16: U1.27 (IO16)
GPIO34: U1.6 (IO34)
GPIO35: U1.7 (IO35)
GPIO36: U1.4 (SENSOR_VP)
GPIO39: U1.5 (SENSOR_VN)
IO5_RST: U1.29 (IO5)
IO17_RCLK: C6.1, R12.1
unnamed: R12.2, U1.28 (IO17)
RXD_ESP: U1.34 (RXD0/IO3)
SCL: J36.1, U1.8 (IO32)
SDA: J36.2, U1.9 (IO33)
TXD_ESP: U1.35 (TXD0/IO1)

Notes on the sheet:
SD Card
Gateway
Gateway ESP32
