MunyratanakBrorn/Smart-Electrical-Energy-Management-System/Hardware/SmartEnergyMag_System PCB deisgn/Power.kicad_sch

## KiCad design Hardware/SmartEnergyMag_System PCB deisgn/Power.kicad_sch (2024-08-28)

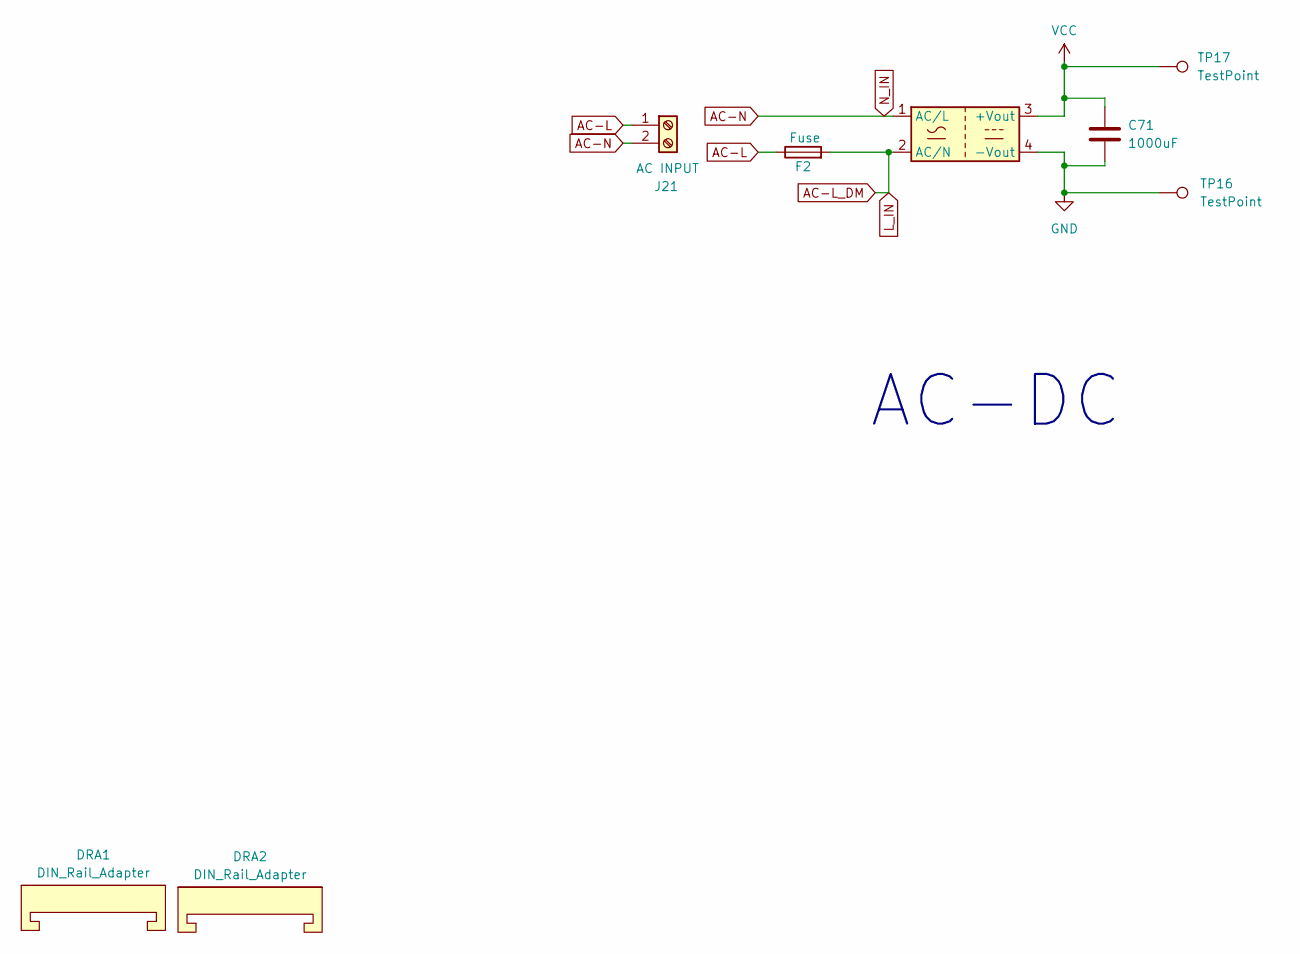
[picture p59: schematic Power.kicad_sch]

Parts:
C71: 1000uF; C_1210_3225Metric
DRA1, DRA2: DIN_Rail_Adapter; DINRailAdapter_3xM3_PhoenixContact_1201578
F2: Fuse; Fuseholder_Cylinder-5x20mm_Schurter_0031_8201_Horizontal_Op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
J21: AC INPUT; Altech_AK300_1x02_P5.00mm_45-Degree
PS1: HLK-12M05A; AC-DC
TP16, TP17: TestPoint; TestPoint_Pad_D1.0mm

Connections:
AC-L: F2.1, J21.1
AC-L_DM: F2.2, PS1.2 (AC/N)
AC-N: J21.2, PS1.1 (AC/L)
GND: C71.1, PS1.4 (-Vout), TP16.1
VCC: C71.2, PS1.3 (+Vout), TP17.1

Notes on the sheet:
AC-DC
