MunyratanakBrorn/Smart-Electrical-Energy-Management-System/Hardware/SmartEnergyMag_System PCB deisgn/RELAY_5CH.kicad_sch

## KiCad design Hardware/SmartEnergyMag_System PCB deisgn/RELAY_5CH.kicad_sch (2024-08-28)

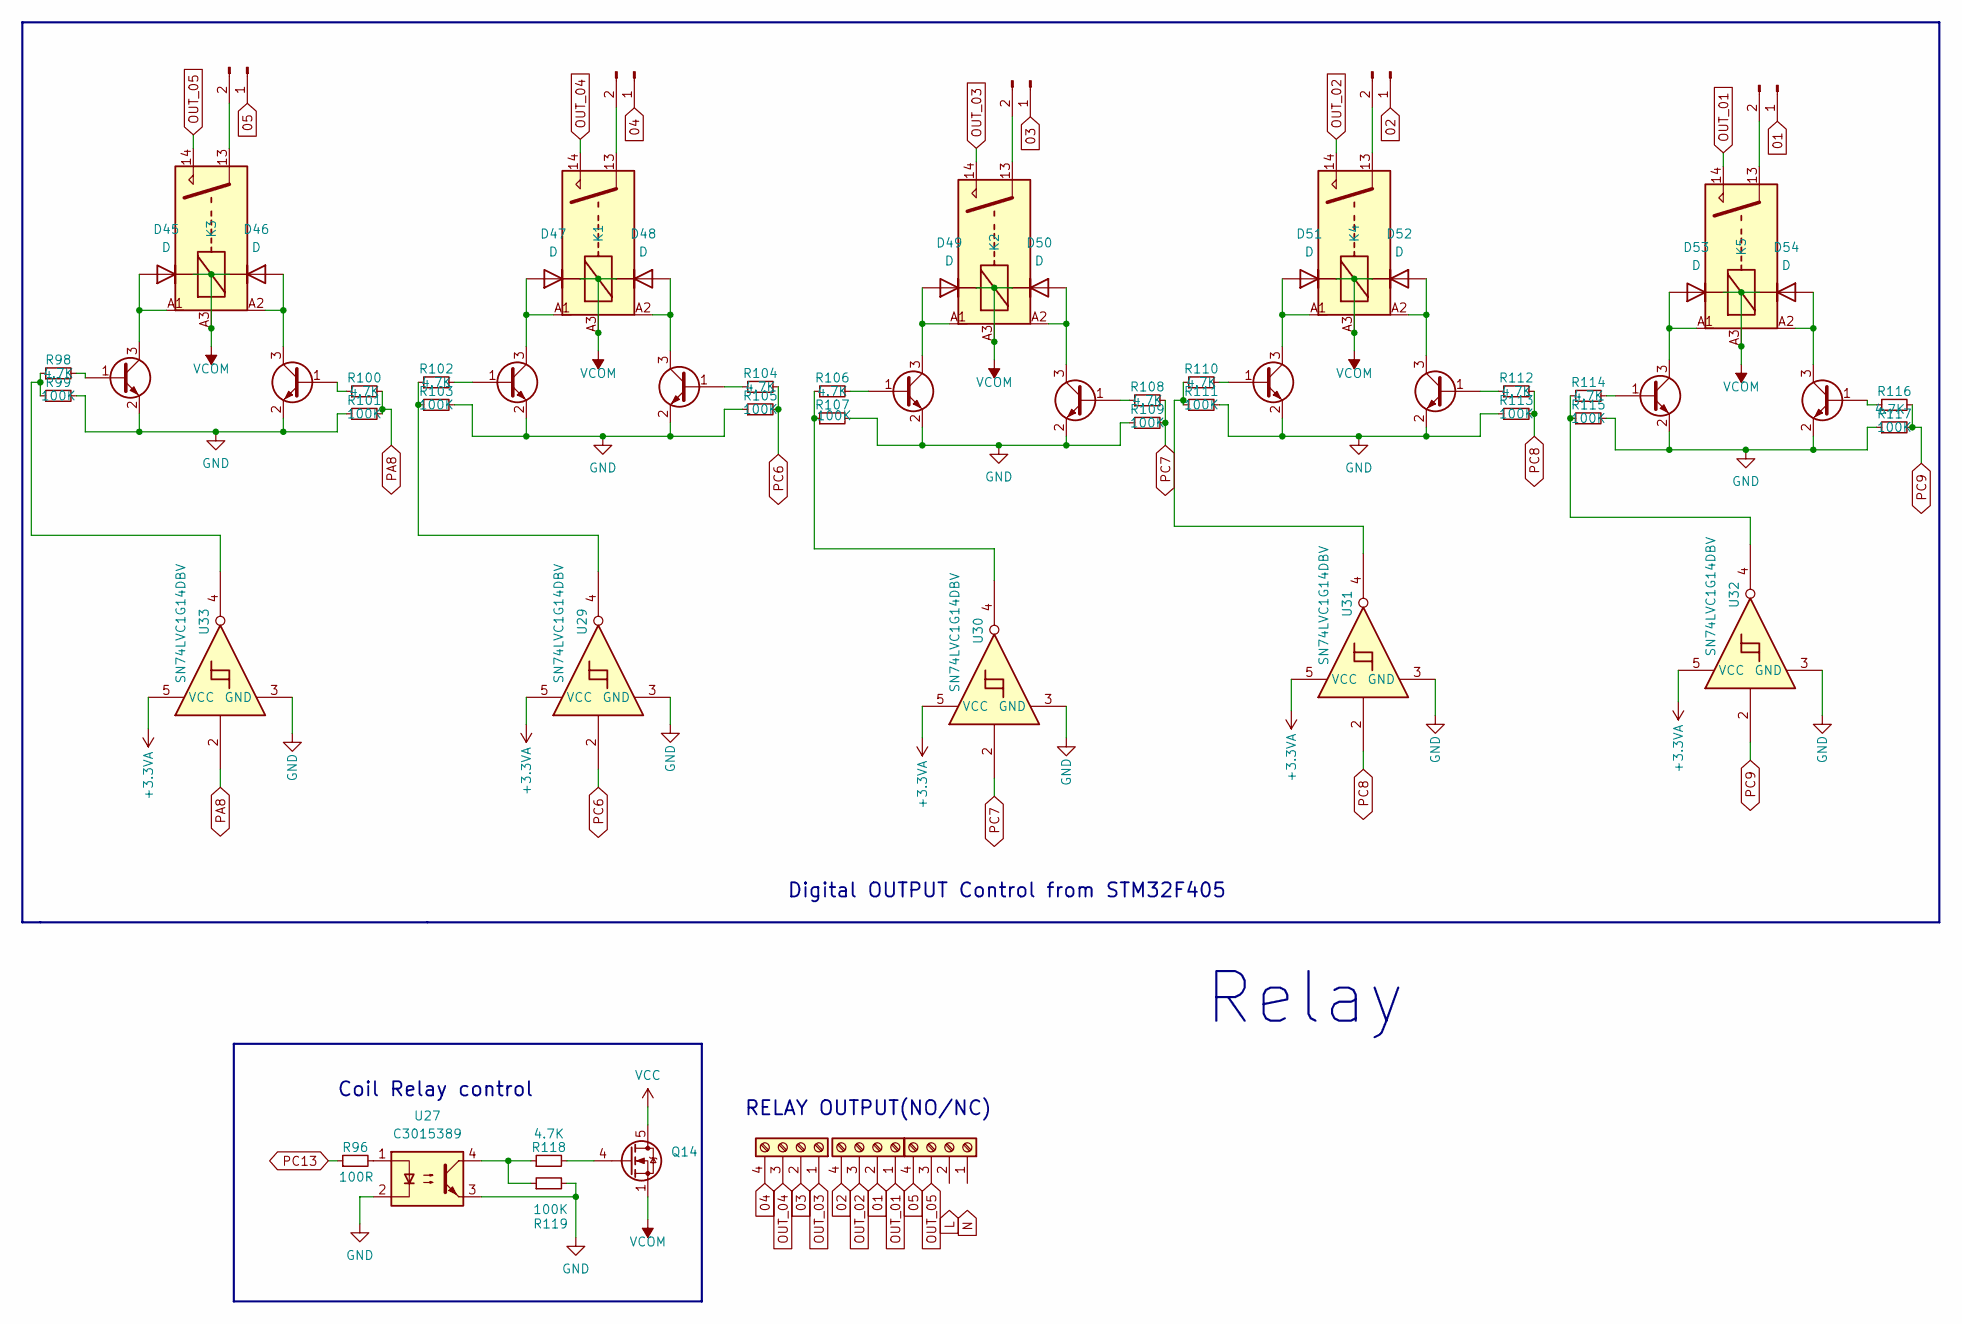
[picture p60: schematic RELAY_5CH.kicad_sch]

Parts:
D45, D46, D47, D48, D49, D50, D51, D52, D53, D54: D; D_SMF
J5, J6, J11: Screw_Terminal_01x04; DBT50G-9.5-4P; JLCPCB Part # C395960
J8, J9, J29, J30, J31: Conn_01x02_Pin; ZHT103
K1, K2, K3, K4, K5: Relay_SPST-NO; K88A
Q4, Q5, Q6, Q7, Q8, Q9, Q10, Q11, Q12, Q13: Q_NPN_BEC; SOT-23
Q14: BSC026N08NS5; TDSON-8-1
R96: 100R; R_0603_1608Metric
R98, R100, R102, R104, R106, R108, R110, R112, R114, R116, R118: 4.7K; R_0603_1608Metric
R99, R101, R103, R105, R107, R109, R111, R113, R115, R117, R119: 100K; R_0603_1608Metric
U27: C3015389; SOP-4_4.4x2.6mm_P1.27mm
U29, U30, U31, U32, U33: SN74LVC1G14DBV; SOT-23-5

Connections:
01: J5.2, J31.1
02: J5.4, J30.1
03: J11.2, J29.1
04: J9.1, J11.4
05: J6.4, J8.1
+3.3VA: U29.5 (VCC), U30.5 (VCC), U31.5 (VCC), U32.5 (VCC), U33.5 (VCC)
GND: Q4.2 (E), Q5.2 (E), Q6.2 (E), Q7.2 (E), Q8.2 (E), Q9.2 (E), Q10.2 (E), Q11.2 (E), Q12.2 (E), Q13.2 (E), R99.2, R101.1, R103.2, R105.1, R107.2, R109.1, R111.2, R113.1, R115.2, R117.1, R119.2, U27.2, U27.3, U29.3 (GND), U30.3 (GND), U31.3 (GND), U32.3 (GND), U33.3 (GND)
unnamed: D45.2 (A), K3.A1, Q4.3 (C)
unnamed: D46.2 (A), K3.A2, Q5.3 (C)
unnamed: D47.2 (A), K1.A1, Q6.3 (C)
unnamed: D48.2 (A), K1.A2, Q7.3 (C)
unnamed: D49.2 (A), K2.A1, Q8.3 (C)
unnamed: D50.2 (A), K2.A2, Q9.3 (C)
unnamed: D51.2 (A), K4.A1, Q10.3 (C)
unnamed: D52.2 (A), K4.A2, Q11.3 (C)
unnamed: D53.2 (A), K5.A1, Q12.3 (C)
unnamed: D54.2 (A), K5.A2, Q13.3 (C)
unnamed: J8.2, K3.13
unnamed: J9.2, K1.13
unnamed: J29.2, K2.13
unnamed: J30.2, K4.13
unnamed: J31.2, K5.13
unnamed: Q4.1 (B), R98.2
unnamed: Q5.1 (B), R100.1
unnamed: Q6.1 (B), R102.2
unnamed: Q7.1 (B), R104.1
unnamed: Q8.1 (B), R106.2
unnamed: Q9.1 (B), R108.1
unnamed: Q10.1 (B), R110.2
unnamed: Q11.1 (B), R112.1
unnamed: Q12.1 (B), R114.2
unnamed: Q13.1 (B), R116.1
unnamed: Q14.4 (G), R118.2
unnamed: R96.2, U27.1
unnamed: R98.1, R99.1, U33.4
unnamed: R102.1, R103.1, U29.4
unnamed: R106.1, R107.1, U30.4
unnamed: R110.1, R111.1, U31.4
unnamed: R114.1, R115.1, U32.4
unnamed: R118.1, R119.1, U27.4
OUT_01: J5.1, K5.14
OUT_02: J5.3, K4.14
OUT_03: J11.1, K2.14
OUT_04: J11.3, K1.14
OUT_05: J6.3, K3.14
PA8: R100.2, R101.2, U33.2
PC6: R104.2, R105.2, U29.2
PC7: R108.2, R109.2, U30.2
PC8: R112.2, R113.2, U31.2
PC9: R116.2, R117.2, U32.2
PC13: R96.1
VCC: Q14.5 (D)
VCOM: D45.1 (K), D46.1 (K), D47.1 (K), D48.1 (K), D49.1 (K), D50.1 (K), D51.1 (K), D52.1 (K), D53.1 (K), D54.1 (K), K1.A3, K2.A3, K3.A3, K4.A3, K5.A3, Q14.1 (S), Q14.2 (S), Q14.3 (S)

Notes on the sheet:
Relay
RELAY OUTPUT(NO/NC)
Digital OUTPUT Control from STM32F405
Coil Relay control
