MunyratanakBrorn/Smart-Electrical-Energy-Management-System/Hardware/SmartEnergyMag_System PCB deisgn/RS485.kicad_sch

## KiCad design Hardware/SmartEnergyMag_System PCB deisgn/RS485.kicad_sch (2024-08-28)

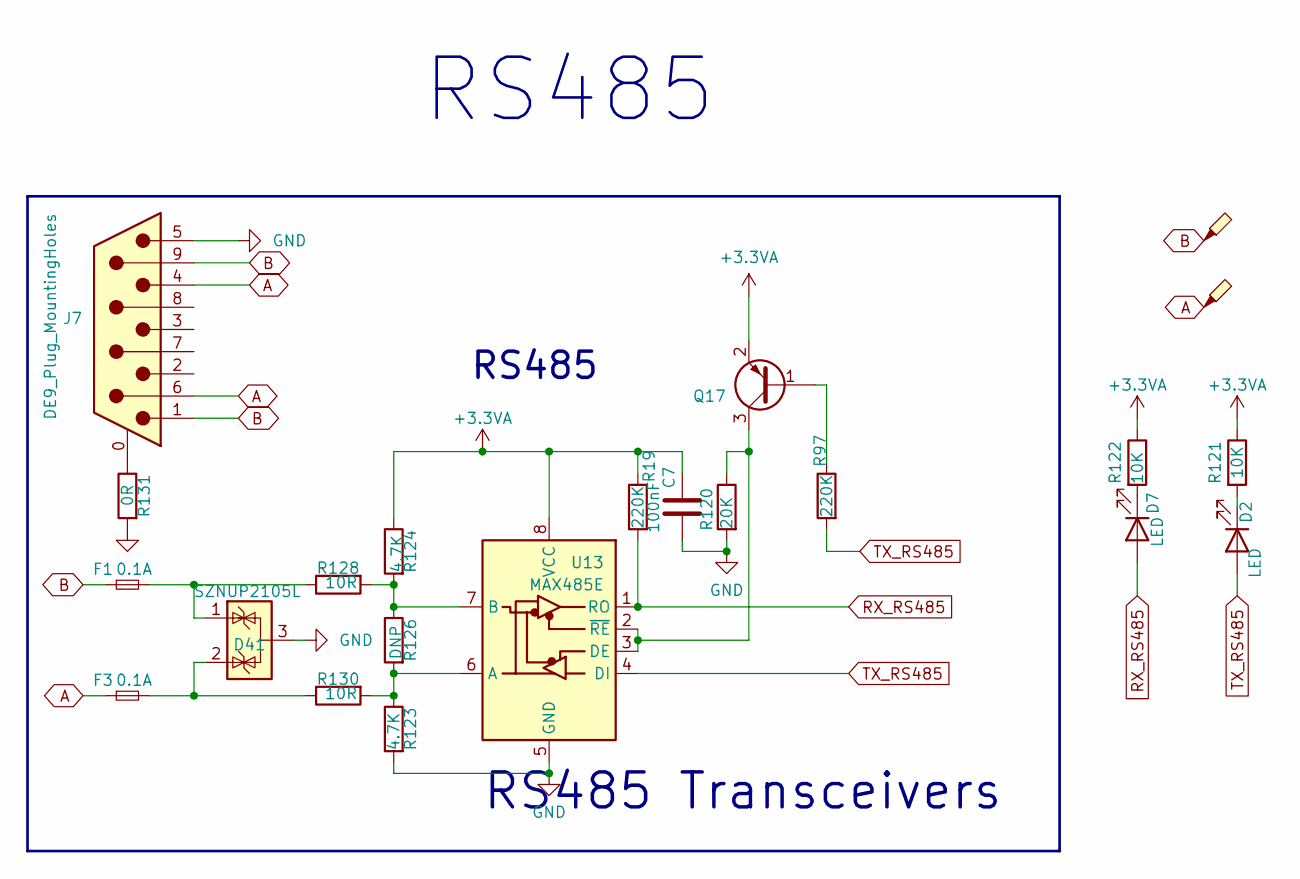
[picture p61: schematic RS485.kicad_sch]

Parts:
C7: 100nF; C_0603_1608Metric
D2, D7: LED; LED_0603_1608Metric
D41: SZNUP2105L; SOT-23
F1, F3: 0.1A; Fuse_1206_3216Metric
J7: DE9_Plug_MountingHoles; DSUB-9_Male_Horizontal_P2.77x2.84mm_EdgePinOffset4.94mm_Hou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
Q17: Q_PNP_BEC; SOT-23
R19, R97: 220K; R_0603_1608Metric
R120: 20K; R_0603_1608Metric
R121, R122: 10K; R_0603_1608Metric
R123, R124: 4.7K; R_0603_1608Metric
R126: DNP; R_0603_1608Metric
R128, R130: 10R; R_0603_1608Metric
R131: 0R; R_0603_1608Metric
TP18, TP19: C5199900; TestPoint_Loop_D1.80mm_Drill1.0mm_Beaded; JLCPCB Part # C5277087
U13: MAX485E; SOIC-8_3.9x4.9mm_P1.27mm

Connections:
+3.3VA: C7.1, Q17.2 (E), R19.1, R121.1, R122.1, R124.1, U13.8 (VCC)
A: F3.1, J7.4, J7.6, TP18.1
B: F1.1, J7.1, J7.9, TP19.1
GND: C7.2, D41.3 (A), J7.5, R120.2, R123.2, R131.2, U13.5 (GND)
unnamed: D2.1 (K), R121.2
unnamed: D7.1 (K), R122.2
unnamed: D41.1 (K), F1.2, R128.1
unnamed: D41.2 (K), F3.2, R130.1
unnamed: J7.0 (PAD), R131.1
unnamed: Q17.1 (B), R97.1
unnamed: Q17.3 (C), R120.1, U13.2 (~RE), U13.3 (DE)
unnamed: R123.1, R126.2, R130.2, U13.6 (A)
unnamed: R124.2, R126.1, R128.2, U13.7 (B)
RX_RS485: D7.2 (A), R19.2, U13.1 (RO)
TX_RS485: D2.2 (A), R97.2, U13.4 (DI)

Notes on the sheet:
RS485 Transceivers
RS485
