MunyratanakBrorn/Smart-Electrical-Energy-Management-System/Hardware/SmartEnergyMag_System PCB deisgn/Realtime.kicad_sch

## KiCad design Hardware/SmartEnergyMag_System PCB deisgn/Realtime.kicad_sch (2024-08-28)

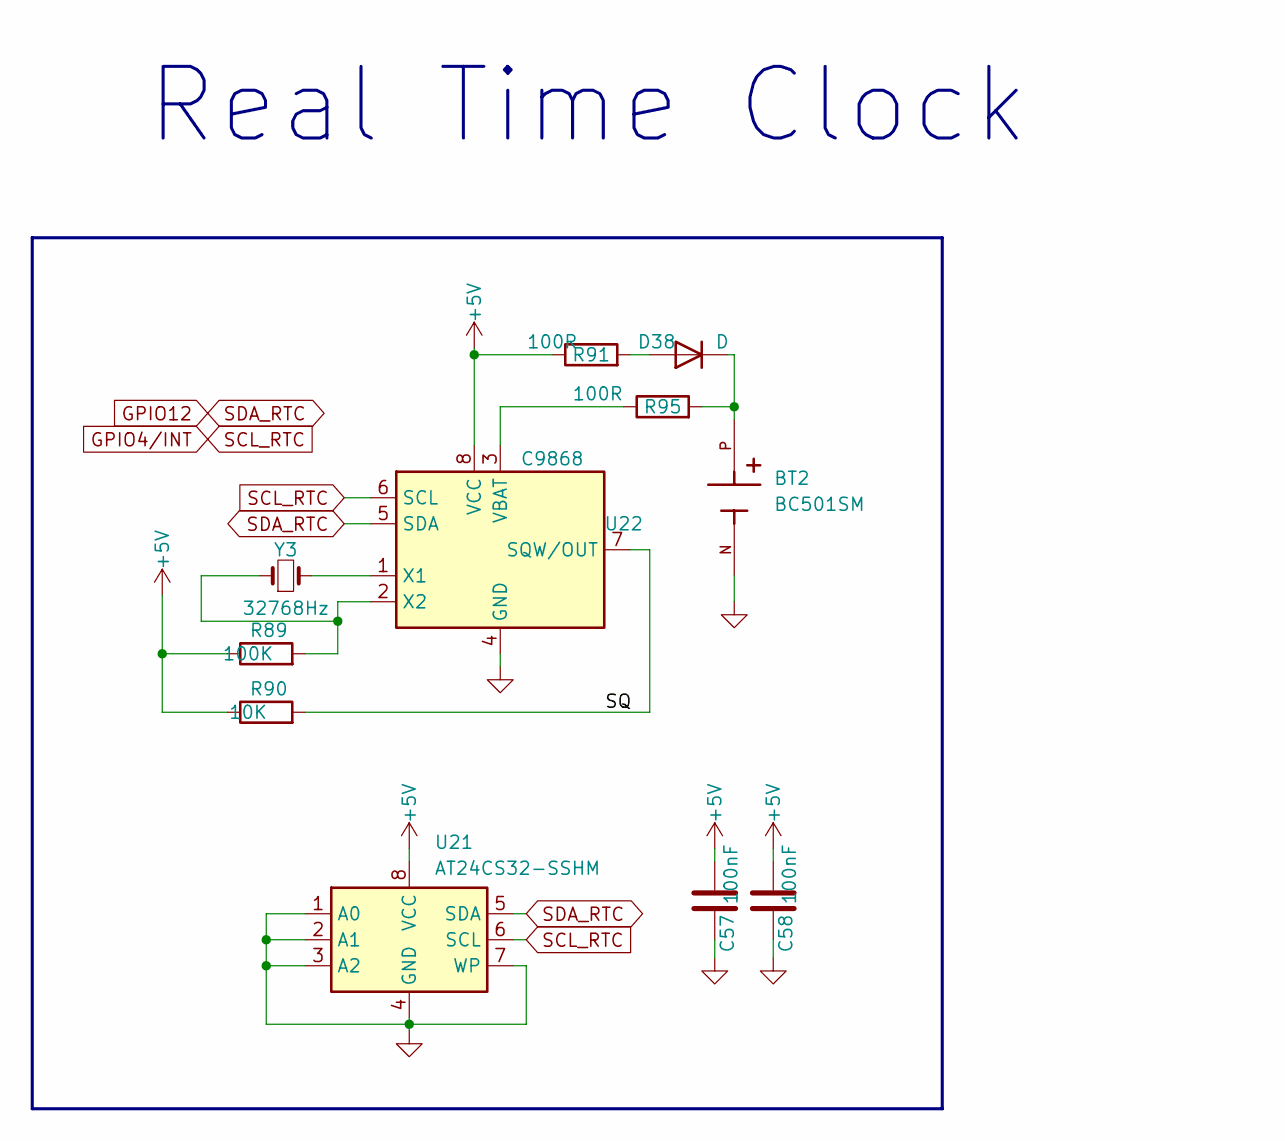
[picture p62: schematic Realtime.kicad_sch]

Parts:
BT2: BC501SM; BAT_BC501SM; PARTREV 10/31/19
C57, C58: 100nF; C_0603_1608Metric
D38: D; D_SMF
R89: 100K; R_0603_1608Metric
R90: 10K; R_0603_1608Metric
R91, R95: 100R; R_0603_1608Metric
U21: AT24CS32-SSHM; SOIC-8_3.9x4.9mm_P1.27mm
U22: C9868; SOIC-8_3.9x4.9mm_P1.27mm
Y3: 32768Hz; Crystal_SMD_3215-2Pin_3.2x1.5mm

Connections:
+5V: C57.2, C58.2, R89.1, R90.1, R91.1, U21.8 (VCC), U22.8 (VCC)
GND: BT2.N, C57.1, C58.1, U21.1 (A0), U21.2 (A1), U21.3 (A2), U21.4 (GND), U21.7 (WP), U22.4 (GND)
GPIO4/INT: U21.6 (SCL), U22.6 (SCL)
GPIO12: U21.5 (SDA), U22.5 (SDA)
unnamed: BT2.P, D38.1 (K), R95.2
unnamed: D38.2 (A), R91.2
unnamed: R89.2, U22.2 (X2), Y3.1
unnamed: R95.1, U22.3 (VBAT)
unnamed: U22.1 (X1), Y3.2
SQ: R90.2, U22.7 (SQW/OUT)

Notes on the sheet:
Real Time Clock
