MunyratanakBrorn/Smart-Electrical-Energy-Management-System/Hardware/SmartEnergyMag_System PCB deisgn/SD_CARD.kicad_sch

## KiCad design Hardware/SmartEnergyMag_System PCB deisgn/SD_CARD.kicad_sch (2024-08-28)

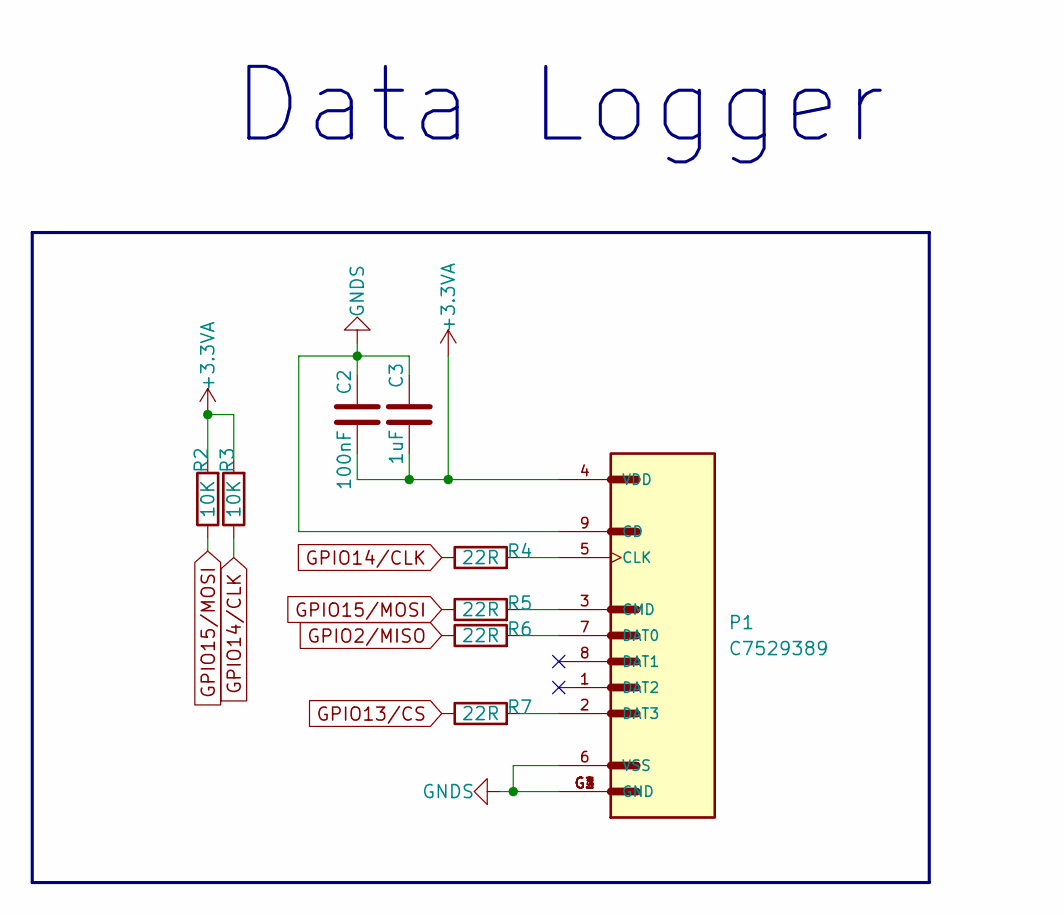
[picture p63: schematic SD_CARD.kicad_sch]

Parts:
C2: 100nF; C_0603_1608Metric
C3: 1uF; C_0603_1608Metric
P1: C7529389; SUNTECH_ST-TF-003A
R2, R3: 10K; R_0603_1608Metric
R4, R5, R6, R7: 22R; R_0603_1608Metric

Connections:
+3.3VA: C2.1, C3.1, P1.4 (VDD), R2.2, R3.2
GNDS: C2.2, C3.2, P1.6 (VSS), P1.9 (CD), P1.G1 (GND), P1.G2 (GND), P1.G3 (GND), P1.G4 (GND)
GPIO2/MISO: R6.1
GPIO13/CS: R7.1
GPIO14/CLK: R3.1, R4.1
GPIO15/MOSI: R2.1, R5.1
unnamed: P1.2 (DAT3), R7.2
unnamed: P1.3 (CMD), R5.2
unnamed: P1.5 (CLK), R4.2
unnamed: P1.7 (DAT0), R6.2

Notes on the sheet:
Data Logger
