MunyratanakBrorn/Smart-Electrical-Energy-Management-System/Hardware/SmartEnergyMag_System PCB deisgn/STM32F405RGTX.kicad_sch

## KiCad design Hardware/SmartEnergyMag_System PCB deisgn/STM32F405RGTX.kicad_sch (2024-08-28)

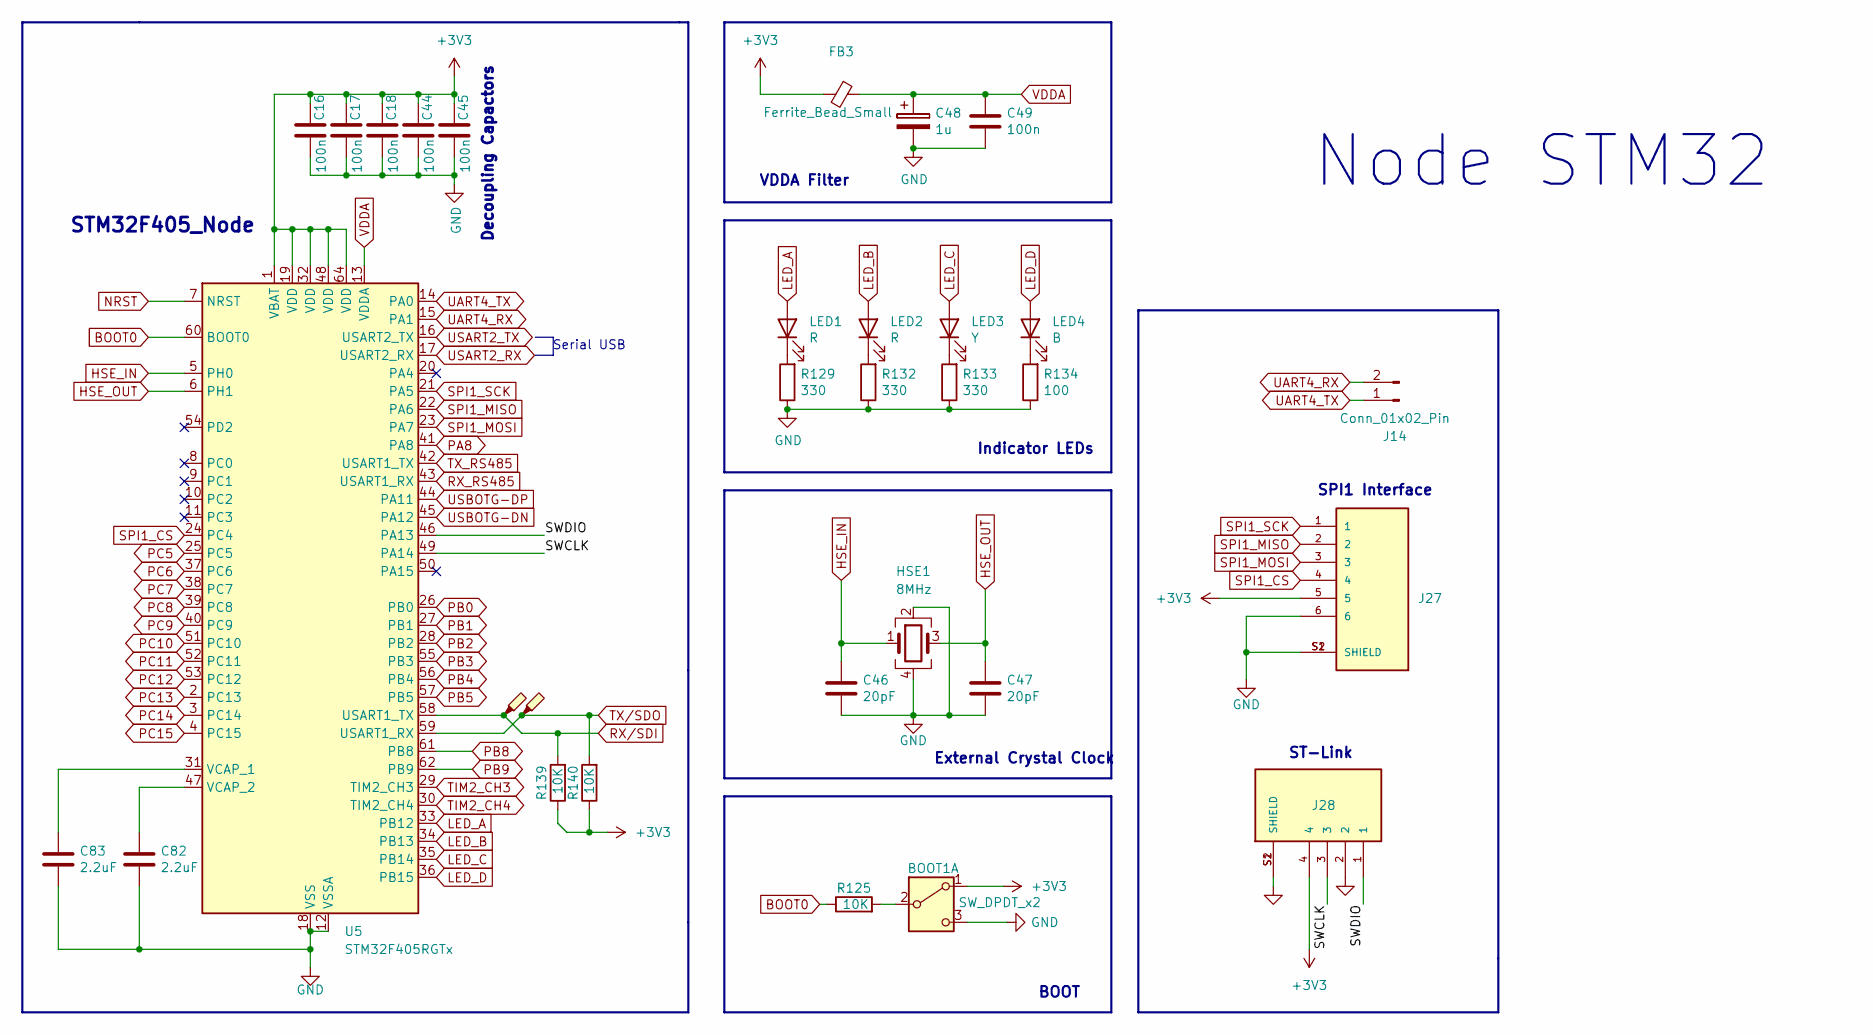
[picture p64: schematic STM32F405RGTX.kicad_sch]

Parts:
BOOT1: SW_DPDT_x2; SW_SPDT_PCM12
C16, C17, C18, C44, C45, C49: 100n; C_0603_1608Metric
C46, C47: 20pF; C_0603_1608Metric
C48: 1u; C_0603_1608Metric
C82, C83: 2.2uF; C_0603_1608Metric
FB3: Ferrite_Bead_Small; L_0603_1608Metric
HSE1: 8MHz; Crystal_SMD_Abracon_ABM8G-4Pin_3.2x2.5mm
J14: Conn_01x02_Pin; JST_XA_B02B-XASK-1_1x02_P2.50mm_Vertical
J27: 0533980671; MOLEX_0533980671; PARTREV A
J28: SM04B-ZESS-TB_LF__SN_; JST_SM04B-ZESS-TB_LF__SN_; PARTREV N/A
LED1, LED2: R; LED_0603_1608Metric
LED3: Y; LED_0603_1608Metric
LED4: B; LED_0603_1608Metric
R125, R139, R140: 10K; R_0402_1005Metric
R129, R132, R133: 330; R_0603_1608Metric
R134: 100; R_0603_1608Metric
TP7, TP8: TestPoint_Probe; TestPoint_Pad_D1.0mm
U5: STM32F405RGTx; LQFP-64_10x10mm_P0.5mm

Connections:
+3V3: BOOT1.1 (A), C16.1, C17.1, C18.1, C44.1, C45.1, FB3.2, J27.5, J28.4, R139.1, R140.1, U5.1 (VBAT), U5.19 (VDD), U5.32 (VDD), U5.48 (VDD), U5.64 (VDD)
BOOT0: R125.1, U5.60 (BOOT0)
GND: BOOT1.3 (C), C16.2, C17.2, C18.2, C44.2, C45.2, C46.2, C47.2, C48.2, C49.2, C82.2, C83.2, HSE1.2, HSE1.4, J27.6, J27.S1 (SHIELD), J27.S2 (SHIELD), J28.2, J28.S1 (SHIELD), J28.S2 (SHIELD), R129.1, R132.1, R133.1, R134.1, U5.12 (VSSA), U5.18 (VSS), U5.63 (VSS)
HSE_IN: C46.1, HSE1.1, U5.5 (PH0)
HSE_OUT: C47.1, HSE1.3, U5.6 (PH1)
LED_A: LED1.2 (A), U5.33 (PB12)
LED_B: LED2.2 (A), U5.34 (PB13)
LED_C: LED3.2 (A), U5.35 (PB14)
LED_D: LED4.2 (A), U5.36 (PB15)
NRST: U5.7 (NRST)
unnamed: BOOT1.2 (B), R125.2
unnamed: C82.1, U5.47 (VCAP_2)
unnamed: C83.1, U5.31 (VCAP_1)
unnamed: LED1.1 (K), R129.2
unnamed: LED2.1 (K), R132.2
unnamed: LED3.1 (K), R133.2
unnamed: LED4.1 (K), R134.2
PA8: U5.41 (PA8)
PB0: U5.26 (PB0)
PB1: U5.27 (PB1)
PB2: U5.28 (PB2)
PB3: U5.55 (PB3)
PB4: U5.56 (PB4)
PB5: U5.57 (PB5)
PB8: U5.61 (PB8)
PB9: U5.62 (PB9)
PC5: U5.25 (PC5)
PC6: U5.37 (PC6)
PC7: U5.38 (PC7)
PC8: U5.39 (PC8)
PC9: U5.40 (PC9)
PC10: U5.51 (PC10)
PC11: U5.52 (PC11)
PC12: U5.53 (PC12)
PC13: U5.2 (PC13)
PC14: U5.3 (PC14)
PC15: U5.4 (PC15)
RX/SDI: R139.2, TP7.1, U5.58 (PB6)
RX_RS485: U5.43 (PA10)
SPI1_CS: J27.4, U5.24 (PC4)
SPI1_MISO: J27.2, U5.22 (PA6)
SPI1_MOSI: J27.3, U5.23 (PA7)
SPI1_SCK: J27.1, U5.21 (PA5)
SWCLK: J28.3, U5.49 (PA14)
SWDIO: J28.1, U5.46 (PA13)
TIM2_CH3: U5.29 (PB10)
TIM2_CH4: U5.30 (PB11)
TX/SDO: R140.2, TP8.1, U5.59 (PB7)
TX_RS485: U5.42 (PA9)
UART4_RX: J14.2, U5.15 (PA1)
UART4_TX: J14.1, U5.14 (PA0)
USART2_RX: U5.17 (PA3)
USART2_TX: U5.16 (PA2)
USBOTG-DN: U5.45 (PA12)
USBOTG-DP: U5.44 (PA11)
VDDA: C48.1, C49.1, FB3.1, U5.13 (VDDA)

Notes on the sheet:
SPI1 Interface
Decoupling Capactors
Node STM32
ST-Link
Serial USB
STM32F405_Node
Indicator LEDs
BOOT
VDDA Filter
External Crystal Clock
