MunyratanakBrorn/Smart-Electrical-Energy-Management-System/Hardware/SmartEnergyMag_System PCB deisgn/USB_UART.kicad_sch

## KiCad design Hardware/SmartEnergyMag_System PCB deisgn/USB_UART.kicad_sch (2024-08-28)

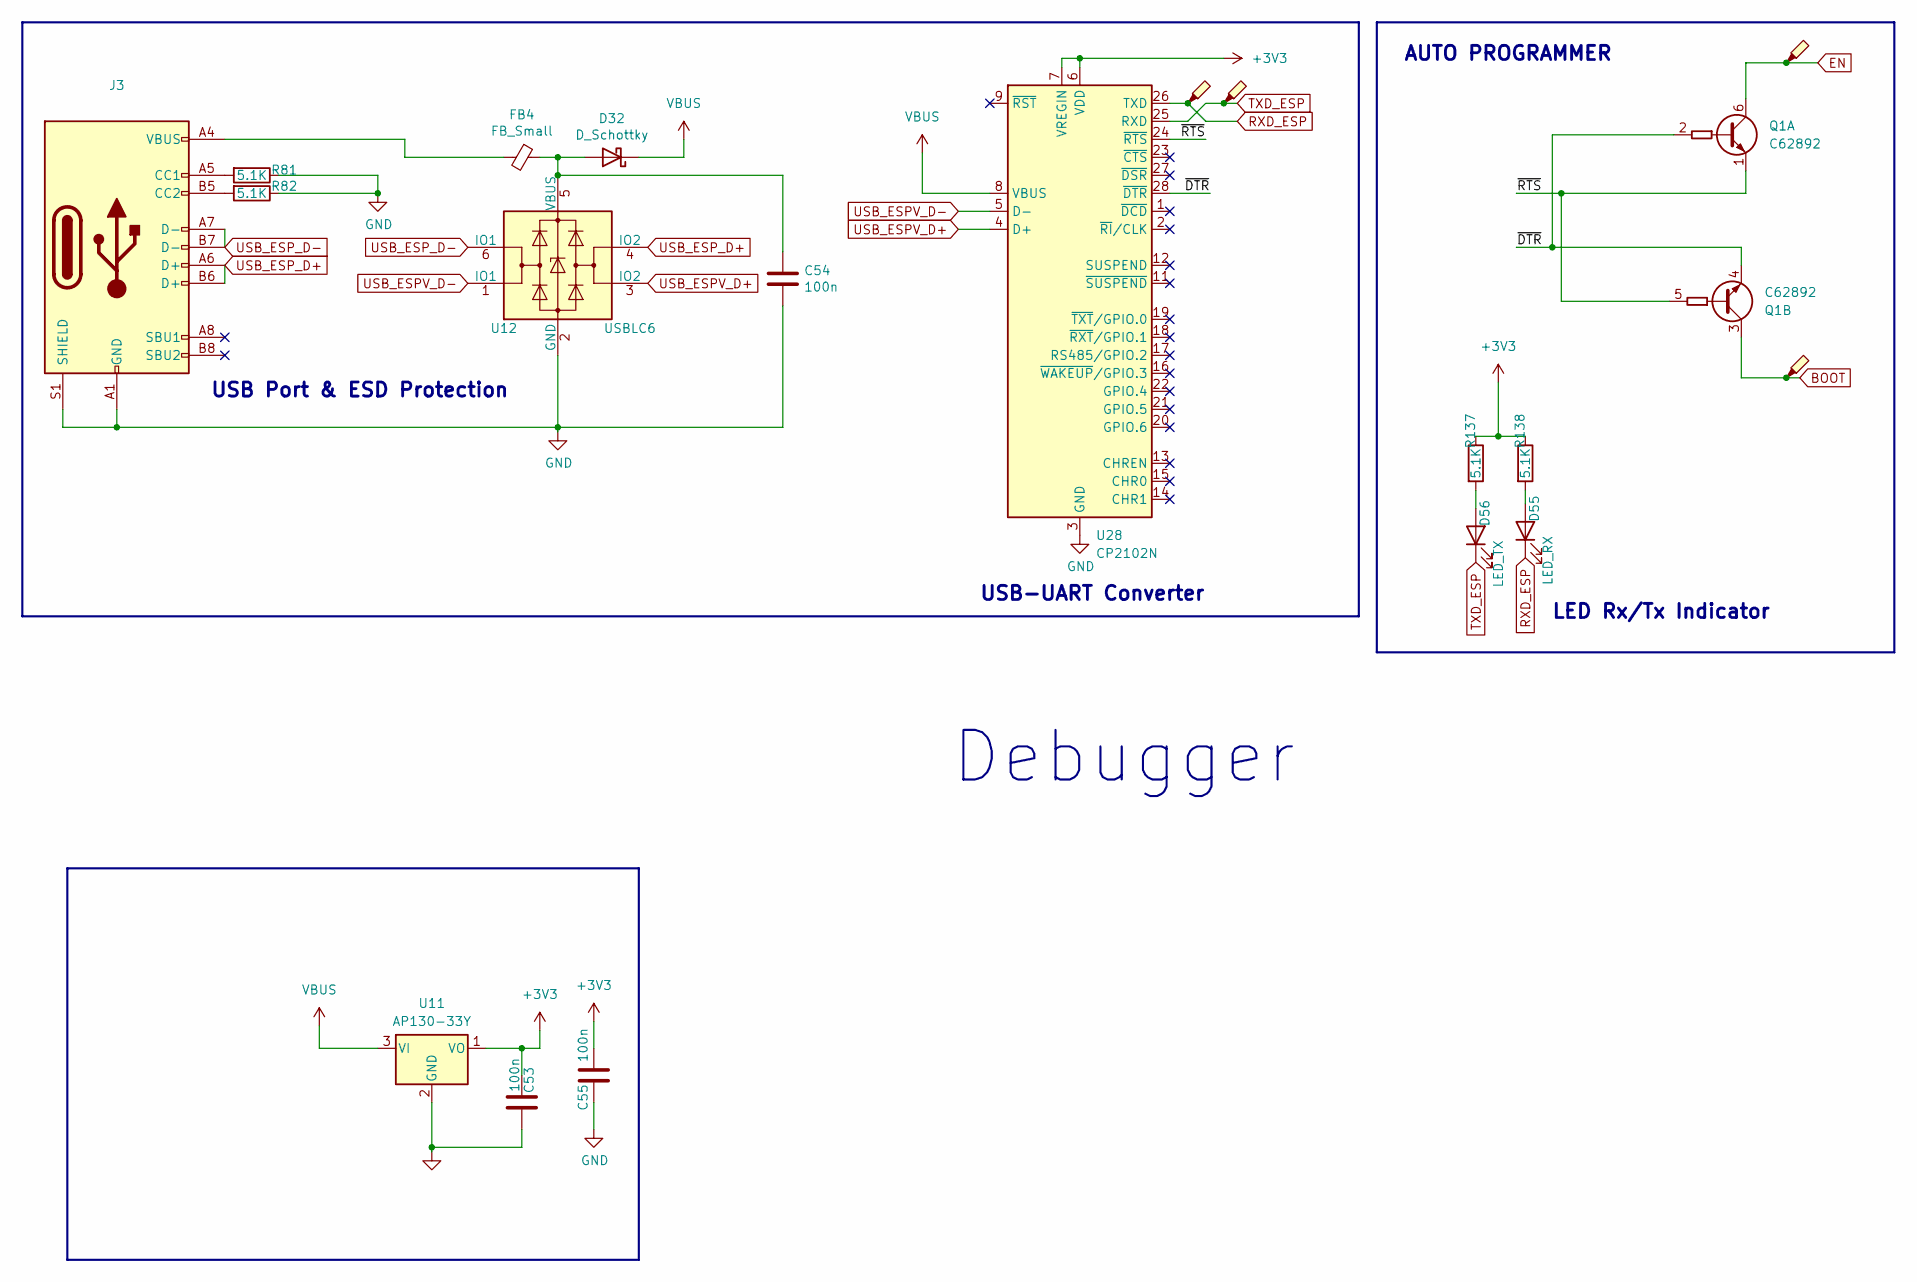
[picture p65: schematic USB_UART.kicad_sch]

Parts:
C53, C54, C55: 100n; C_0603_1608Metric
D32: D_Schottky; D_SOD-323
D55: LED_RX; LED_0603_1608Metric
D56: LED_TX; LED_0603_1608Metric
FB4: FB_Small; L_0603_1608Metric
J3: USB_C_Receptacle_USB2.0_16P; USB_C_Receptacle_G-Switch_GT-USB-7010ASV
Q1: C62892; SOT-363_SC-70-6
R81, R82, R137, R138: 5.1K; R_0603_1608Metric
TP1, TP2, TP3, TP4: TestPoint_Probe; TestPoint_Pad_D1.0mm
U11: AP130-33Y; SOT-89-3
U12: USBLC6; SOT-23-6
U28: CP2102N; QFN-28-1EP_5x5mm_P0.5mm_EP3.1x3.1mm_ThermalVias

Connections:
+3V3: C53.2, C55.1, R137.1, R138.1, U11.1 (VO), U28.6 (VDD), U28.7 (VREGIN)
BOOT: Q1.3 (C2), TP1.1
EN: Q1.6 (C1), TP2.1
GND: C53.1, C54.2, C55.2, J3.A1 (GND), J3.A12 (GND), J3.B1 (GND), J3.B12 (GND), J3.S1 (SHIELD), R81.1, R82.1, U11.2 (GND), U12.2 (GND), U28.3 (GND), U28.29 (GND)
unnamed: C54.1, D32.2 (A), FB4.1, U12.5 (VBUS)
unnamed: D55.2 (A), R138.2
unnamed: D56.2 (A), R137.2
unnamed: FB4.2, J3.A4 (VBUS), J3.A9 (VBUS), J3.B4 (VBUS), J3.B9 (VBUS)
unnamed: J3.A5 (CC1), R81.2
unnamed: J3.B5 (CC2), R82.2
RXD_ESP: D55.1 (K), TP4.1, U28.26 (TXD)
TXD_ESP: D56.1 (K), TP3.1, U28.25 (RXD)
USB_ESPV_D+: U12.3 (IO2), U28.4 (D+)
USB_ESPV_D-: U12.1 (IO1), U28.5 (D-)
USB_ESP_D+: J3.A6 (D+), J3.B6 (D+), U12.4 (IO2)
USB_ESP_D-: J3.A7 (D-), J3.B7 (D-), U12.6 (IO1)
VBUS: D32.1 (K), U11.3 (VI), U28.8 (VBUS)
~DTR: Q1.2 (B1), Q1.4 (E2), U28.28 (~DTR)
~RTS: Q1.1 (E1), Q1.5 (B2), U28.24 (~RTS)

Notes on the sheet:
AUTO PROGRAMMER
USB Port & ESD Protection
USB-UART Converter
LED Rx/Tx Indicator
Debugger
