MunyratanakBrorn/Smart-Electrical-Energy-Management-System/Hardware/SmartEnergyMag_System PCB deisgn/output.kicad_sch

## KiCad design Hardware/SmartEnergyMag_System PCB deisgn/output.kicad_sch (2024-08-28)

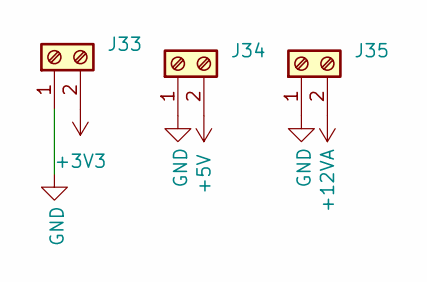
[picture p66: schematic output.kicad_sch]

Parts:
J33, J34, J35: Screw_Terminal_01x02; Altech_AK300_1x02_P5.00mm_45-Degree

Connections:
+3V3: J33.2
+5V: J34.2
+12VA: J35.2
GND: J33.1, J34.1, J35.1
