MunyratanakBrorn/Smart-Electrical-Energy-Management-System/Hardware/SmartEnergyMag_System PCB deisgn/uart.kicad_sch

## KiCad design Hardware/SmartEnergyMag_System PCB deisgn/uart.kicad_sch (2024-08-28)

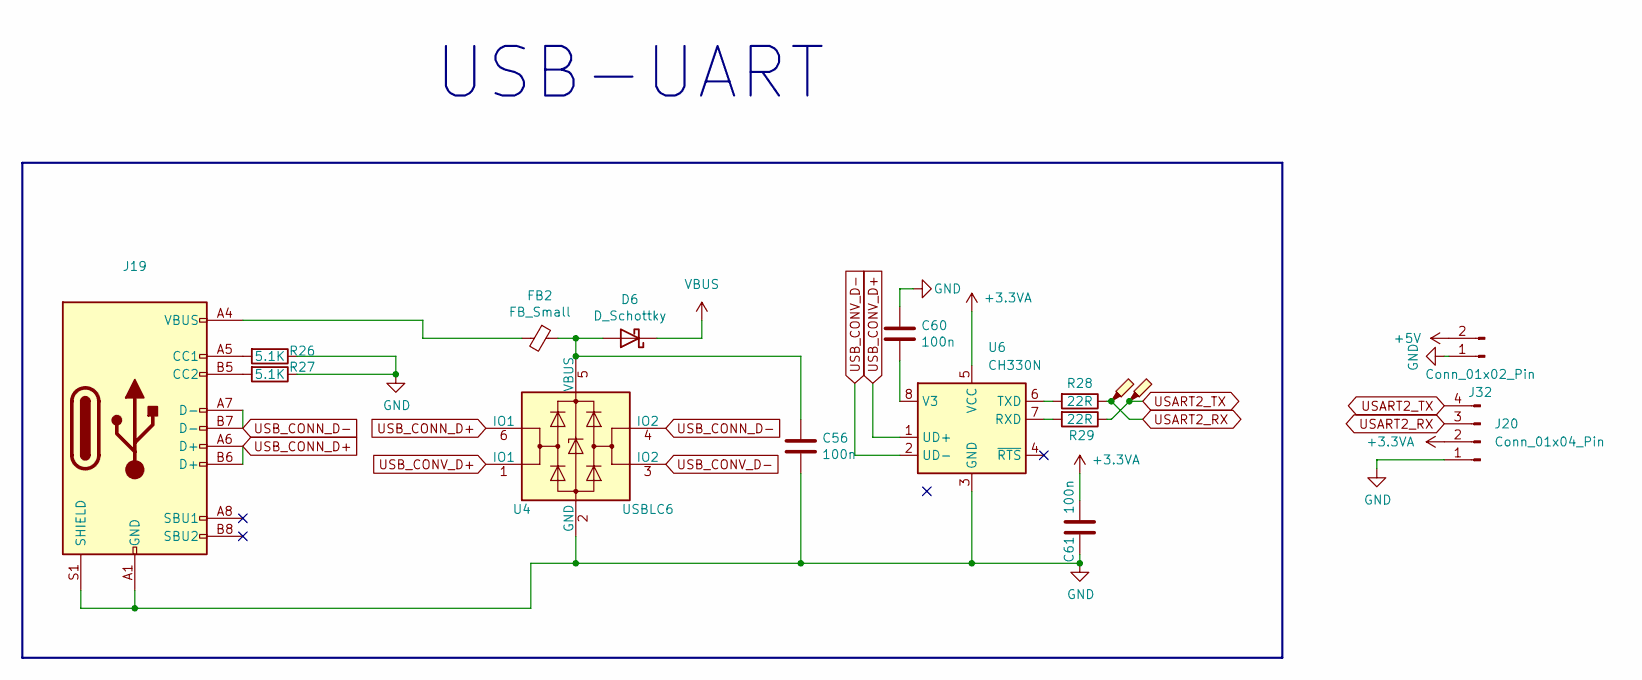
[picture p67: schematic uart.kicad_sch]

Parts:
C56, C60, C61: 100n; C_0603_1608Metric
D6: D_Schottky; D_SOD-323
FB2: FB_Small; L_0603_1608Metric
J19: C7506797; USB_C_Receptacle_G-Switch_GT-USB-7010ASV; JLCPCB Part # C7506797
J20: Conn_01x04_Pin; JST_XA_B04B-XASK-1_1x04_P2.50mm_Vertical
J32: Conn_01x02_Pin; JST_XA_B02B-XASK-1_1x02_P2.50mm_Vertical
R26, R27: 5.1K; R_0603_1608Metric
R28, R29: 22R; R_0603_1608Metric
TP5, TP6: TestPoint_Probe; TestPoint_Pad_D1.0mm
U4: USBLC6; SOT-23-6
U6: CH330N; SOIC-8_3.9x4.9mm_P1.27mm

Connections:
+3.3VA: C61.1, J20.2, U6.5 (VCC)
+5V: J32.2
GND: C56.2, C60.1, C61.2, J19.A1 (GND), J19.A12 (GND), J19.B1 (GND), J19.B12 (GND), J19.S1 (SHIELD), J20.1, J32.1, R26.1, R27.1, U4.2 (GND), U6.3 (GND)
unnamed: C56.1, D6.2 (A), FB2.1, U4.5 (VBUS)
unnamed: C60.2, U6.8 (V3)
unnamed: FB2.2, J19.A4 (VBUS), J19.A9 (VBUS), J19.B4 (VBUS), J19.B9 (VBUS)
unnamed: J19.A5 (CC1), R26.2
unnamed: J19.B5 (CC2), R27.2
unnamed: R28.2, U6.6 (TXD)
unnamed: R29.2, U6.7 (RXD)
USART2_RX: J20.3, R28.1, TP5.1
USART2_TX: J20.4, R29.1, TP6.1
USB_CONN_D+: J19.A6 (D+), J19.B6 (D+), U4.6 (IO1)
USB_CONN_D-: J19.A7 (D-), J19.B7 (D-), U4.4 (IO2)
USB_CONV_D+: U4.1 (IO1), U6.1 (UD+)
USB_CONV_D-: U4.3 (IO2), U6.2 (UD-)
VBUS: D6.1 (K)

Notes on the sheet:
USB-UART
