MunyratanakBrorn/Smart-Electrical-Energy-Management-System/Hardware/SmartEnergyMag_System PCB deisgn/untitled.kicad_sch

## KiCad design Hardware/SmartEnergyMag_System PCB deisgn/untitled.kicad_sch (2024-08-28)

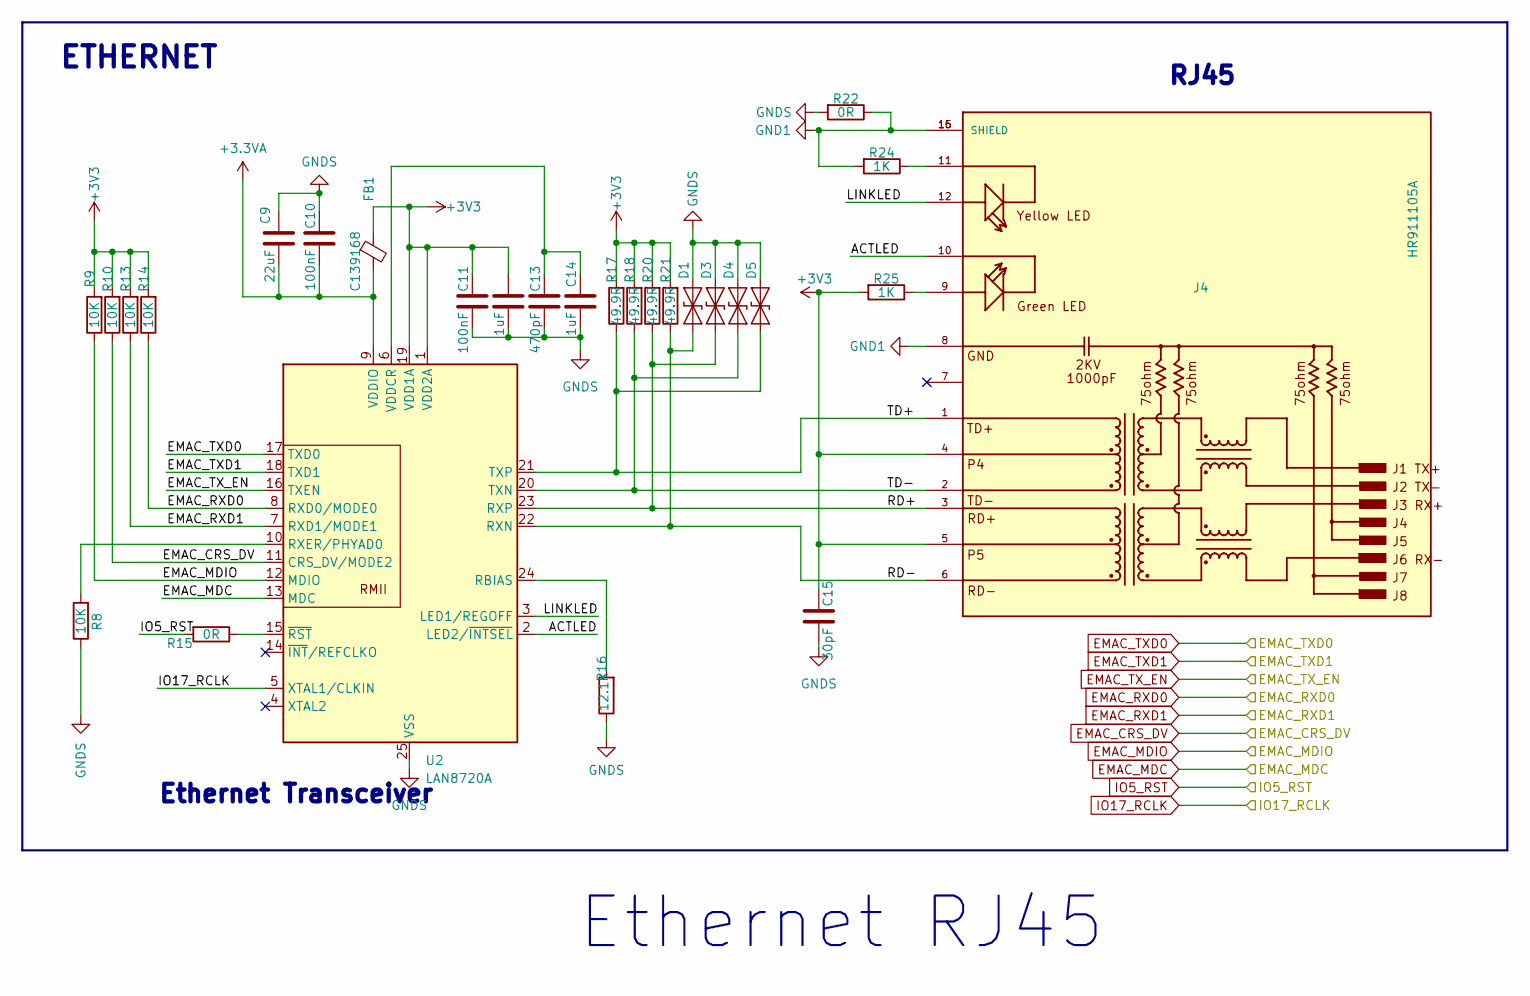
[picture p68: schematic untitled.kicad_sch]

Parts:
C9: 22uF; C_0805_2012Metric
C10: 100nF; C_0603_1608Metric
C11: 100nF; C_0402_1005Metric
C12: 1uF; C_0402_1005Metric
C13: 470pF; C_0603_1608Metric
C14: 1uF; C_0603_1608Metric
C15: 30pF; C_0603_1608Metric
D1, D3, D4, D5: ESD9B3.3ST5G; D_SOD-923
FB1: C139168; L_0805_2012Metric
J4: HR911105A; HANRUN_HR911105A; PARTREV A
R8, R9, R10, R13, R14: 10K; R_0402_1005Metric
R15: 0R; R_0402_1005Metric
R16: 12.1K; R_0402_1005Metric
R17, R18, R20, R21: 49.9R; R_0603_1608Metric
R22: 0R; R_0603_1608Metric
R24, R25: 1K; R_0603_1608Metric
U2: LAN8720A; VQFN-24-1EP_4x4mm_P0.5mm_EP2.5x2.5mm_ThermalVias

Connections:
+3.3VA: C9.2, C10.1, FB1.2, U2.9 (VDDIO)
+3V3: C11.2, C12.2, C15.1, FB1.1, J4.4, J4.5, R9.2, R10.2, R13.2, R14.2, R17.2, R18.2, R20.2, R21.2, R25.2, U2.1 (VDD2A), U2.19 (VDD1A)
ACTLED: J4.10, U2.2 (LED2/~INTSEL)
EMAC_CRS_DV: R10.1, U2.11 (CRS_DV/MODE2)
EMAC_MDC: U2.13 (MDC)
EMAC_MDIO: R9.1, U2.12 (MDIO)
EMAC_RXD0: R14.1, U2.8 (RXD0/MODE0)
EMAC_RXD1: R13.1, U2.7 (RXD1/MODE1)
EMAC_TXD0: U2.17 (TXD0)
EMAC_TXD1: U2.18 (TXD1)
EMAC_TX_EN: U2.16 (TXEN)
GND1: J4.8, J4.15 (SHIELD), J4.16 (SHIELD), R22.1, R24.2
GNDS: C9.1, C10.2, C11.1, C12.1, C13.1, C14.1, C15.2, D1.2 (A2), D3.2 (A2), D4.2 (A2), D5.2 (A2), R8.1, R16.1, R22.2, U2.25 (VSS)
IO5_RST: R15.2
IO17_RCLK: U2.5 (XTAL1/CLKIN)
LINKLED: J4.12, U2.3 (LED1/REGOFF)
unnamed: C13.2, C14.2, U2.6 (VDDCR)
unnamed: J4.9, R25.1
unnamed: J4.11, R24.1
unnamed: R8.2, U2.10 (RXER/PHYAD0)
unnamed: R15.1, U2.15 (~RST)
unnamed: R16.2, U2.24 (RBIAS)
RD+: D3.1 (A1), J4.3, R20.1, U2.23 (RXP)
RD-: D1.1 (A1), J4.6, R21.1, U2.22 (RXN)
TD+: D5.1 (A1), J4.1, R17.1, U2.21 (TXP)
TD-: D4.1 (A1), J4.2, R18.1, U2.20 (TXN)

Notes on the sheet:
Ethernet Transceiver
ETHERNET
Ethernet RJ45
RJ45
